td0g/high_speed_flash/MK1_Edgerton/STL/LED Clamp.STL

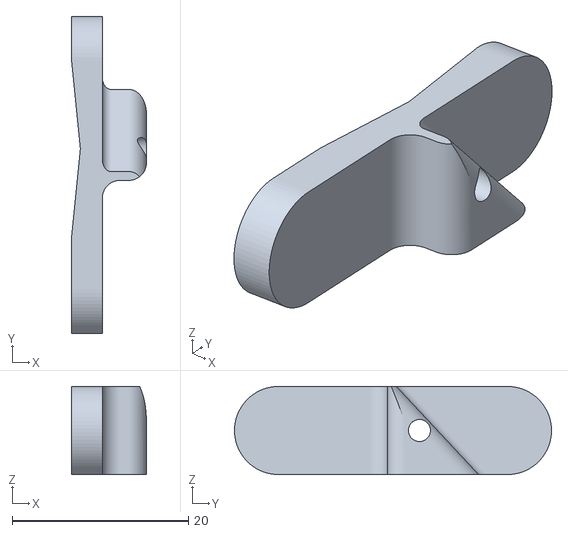
[picture p15: CAD file, 2020-08-31]
MK1_Edgerton/STL/LED Clamp.STL
8.50 x 36.0 x 10.0
