td0g/high_speed_flash/Test Data/2020-08-01/105mm Test/066_Nikon SB-800_64_1.png

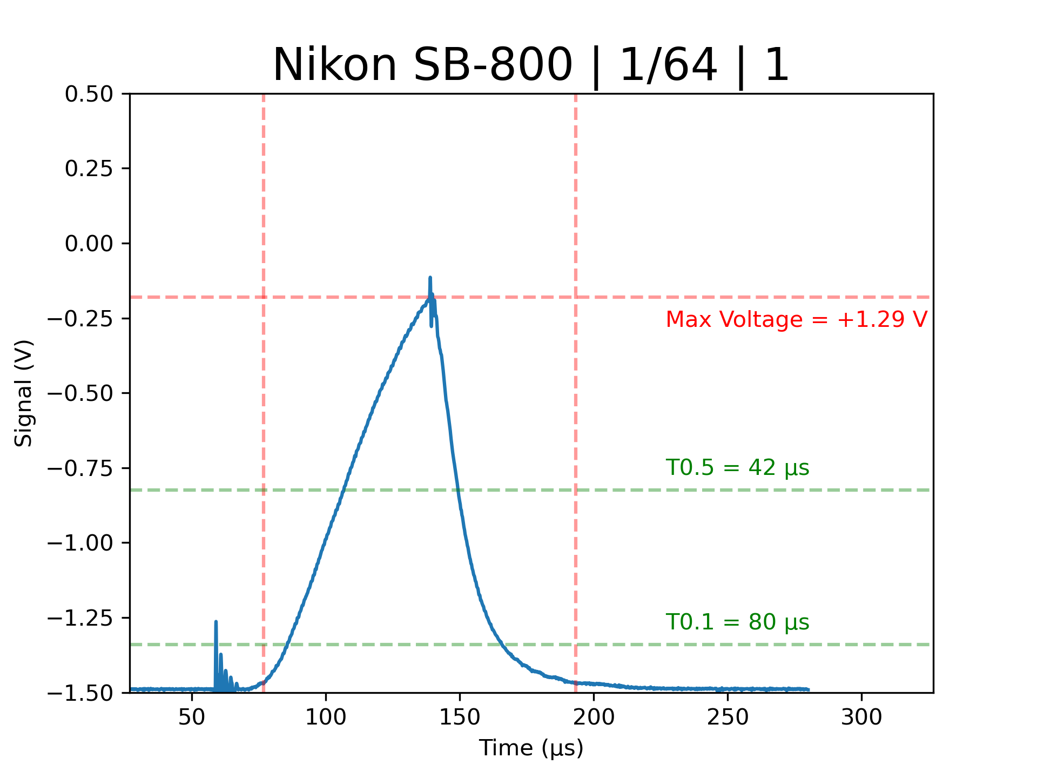
Test Data/2020-08-01/105mm Test/066_Nikon SB-800_64_1.png
