td0g/high_speed_flash/Test Data/2020-08-01/105mm Test/076_Nikon SB-800_32_2.png

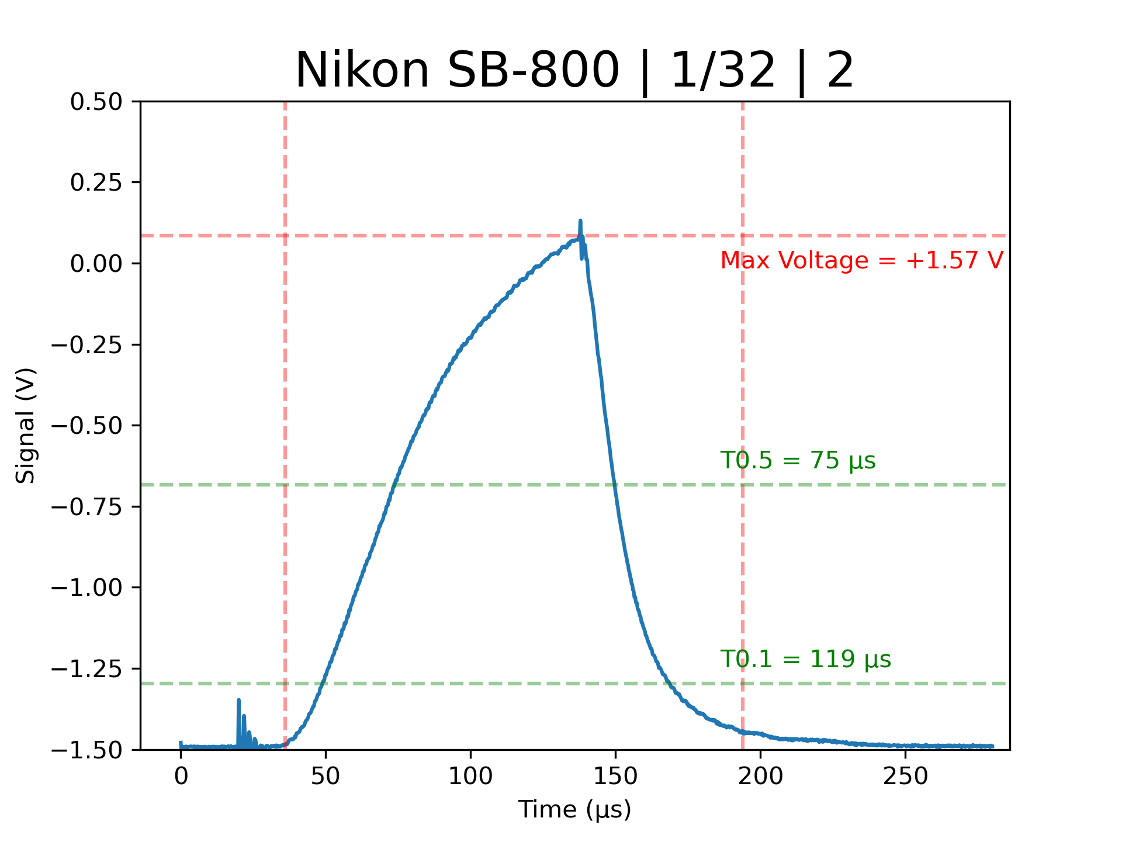
Test Data/2020-08-01/105mm Test/076_Nikon SB-800_32_2.png
