td0g/high_speed_flash/Test Data/2020-08-01/105mm Test/079_Nikon SB-800 105mm_128_1.png

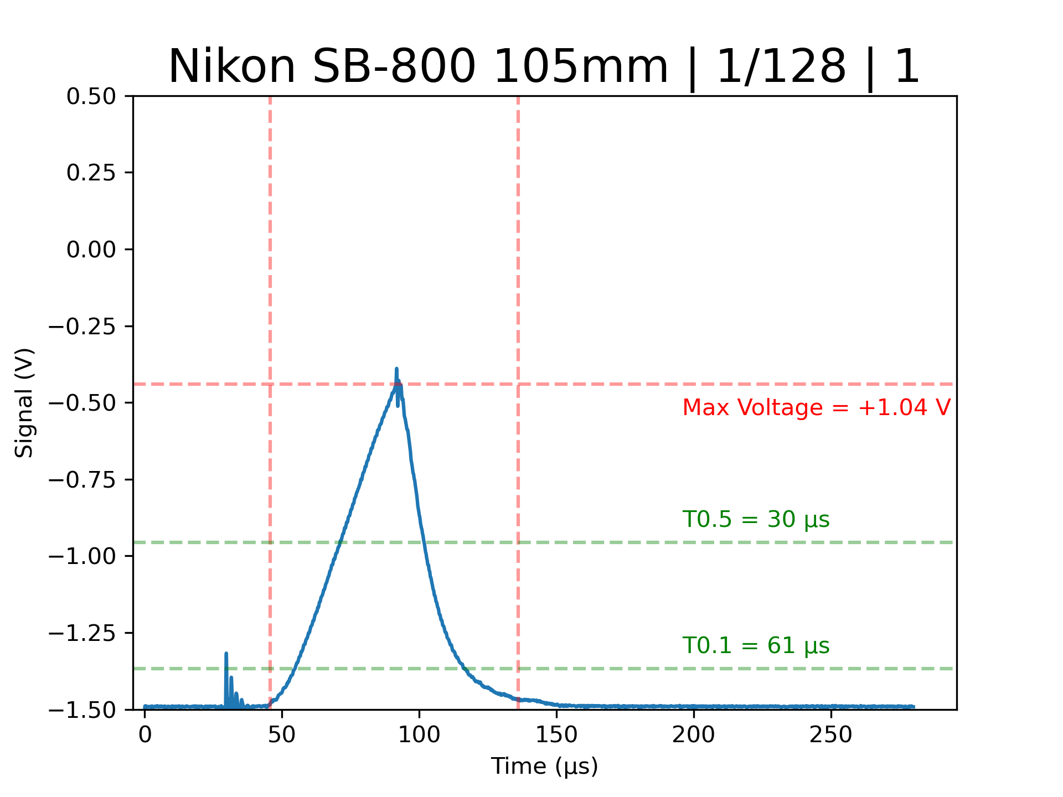
Test Data/2020-08-01/105mm Test/079_Nikon SB-800 105mm_128_1.png
