td0g/high_speed_flash/Test Data/2020-08-01/105mm Test/087_Nikon SB-800 105mm_16_1.png

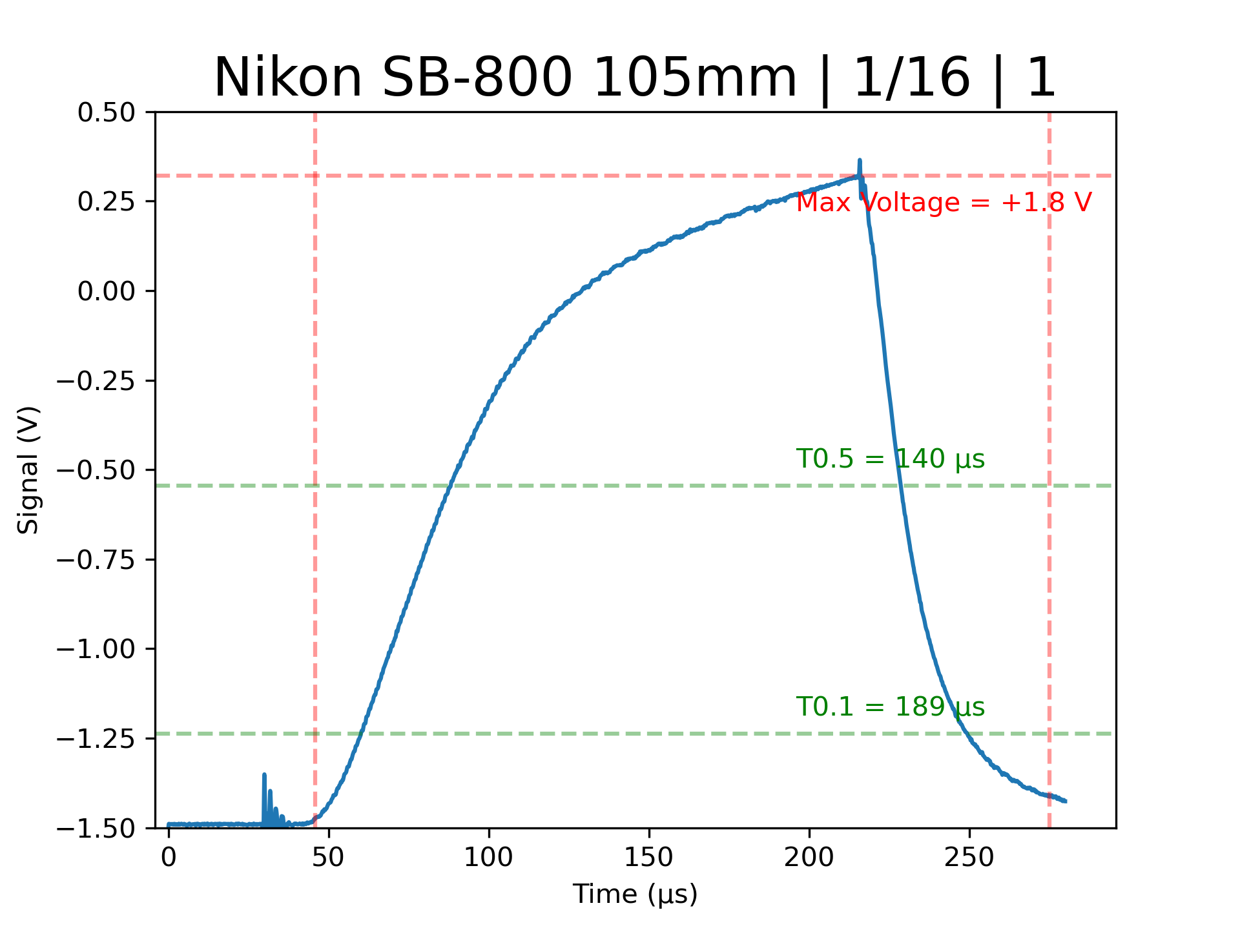
Test Data/2020-08-01/105mm Test/087_Nikon SB-800 105mm_16_1.png
