td0g/high_speed_flash/Test Data/2020-08-01/105mm Test/_MODEL Nikon SB-800 105mm.png

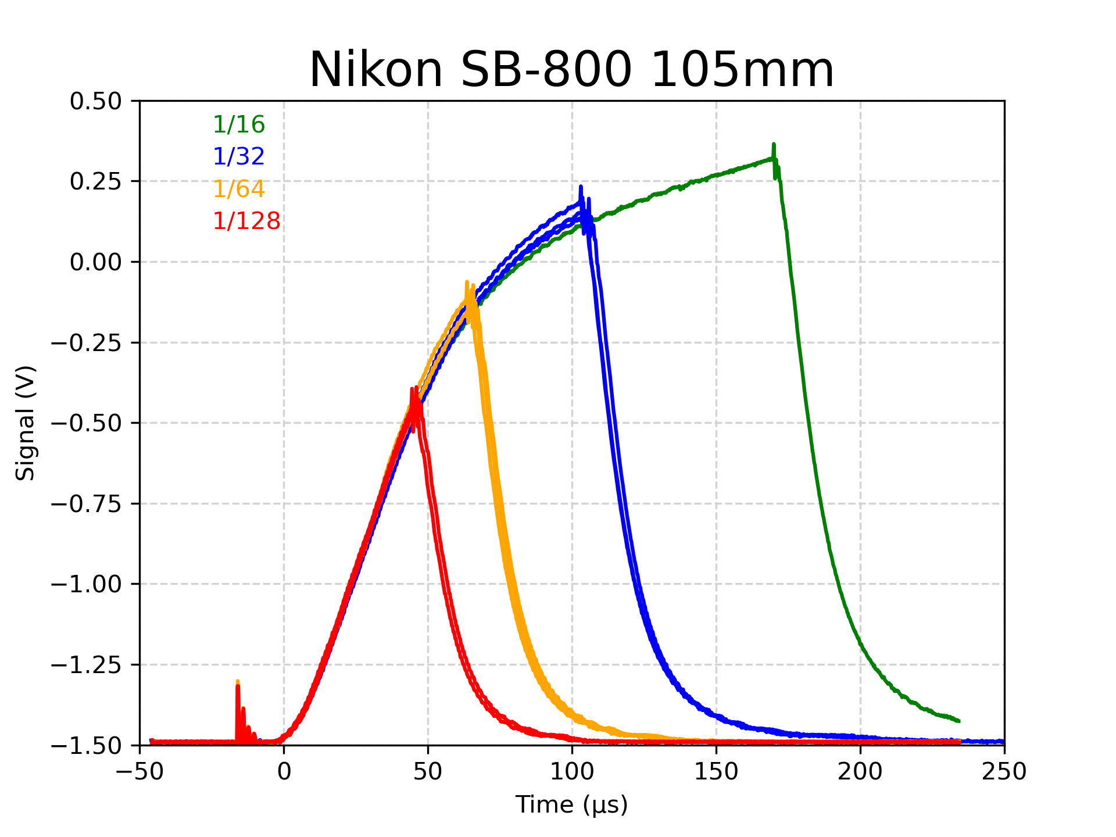
Test Data/2020-08-01/105mm Test/_MODEL Nikon SB-800 105mm.png
