td0g/high_speed_flash/Test Data/2020-08-01/105mm Test/_POWER 3.png

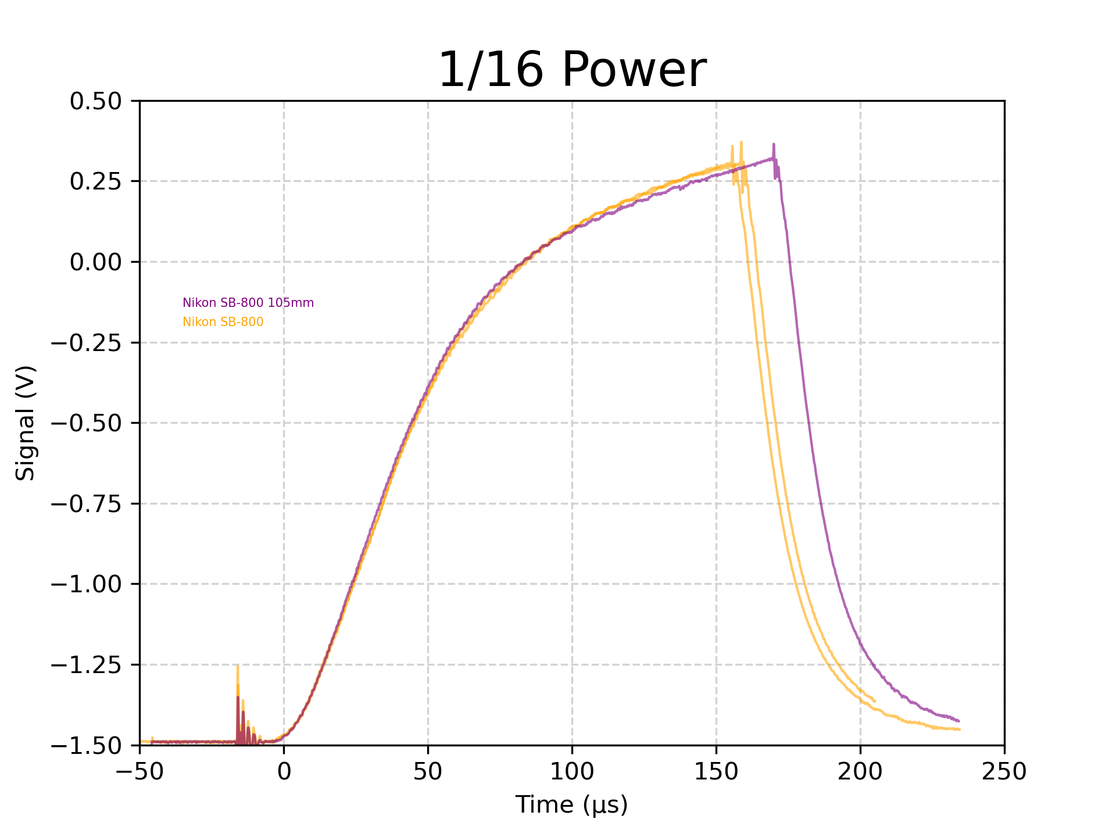
Test Data/2020-08-01/105mm Test/_POWER 3.png
