td0g/high_speed_flash/Test Data/2020-08-01/Removed/002_Nikon SB-800 wCactus_LO_2.png

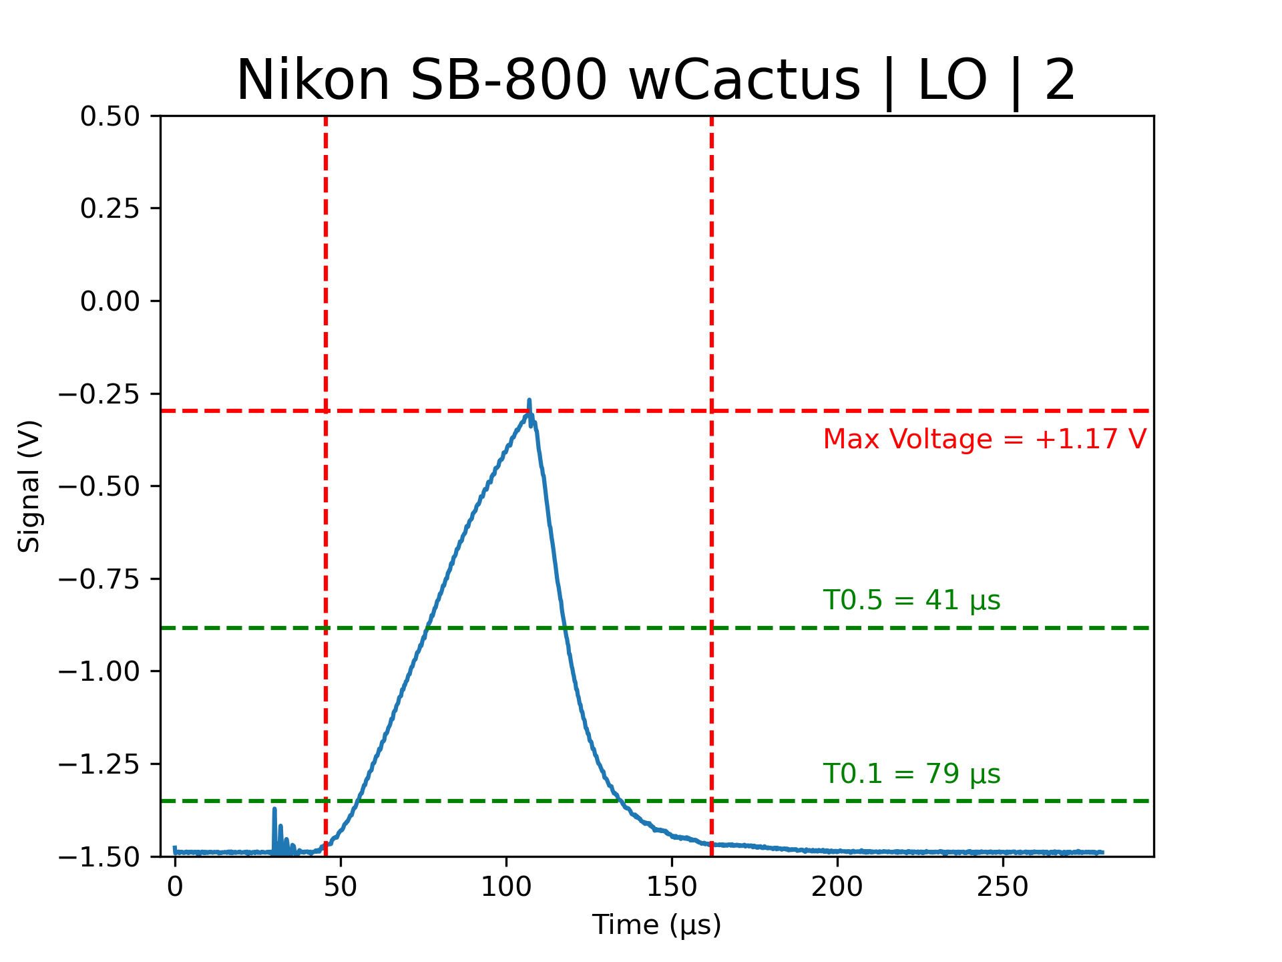
Test Data/2020-08-01/Removed/002_Nikon SB-800 wCactus_LO_2.png
