td0g/high_speed_flash/Test Data/2020-08-01/Removed/004_Nikon SB-800 wCactus_128_1.png

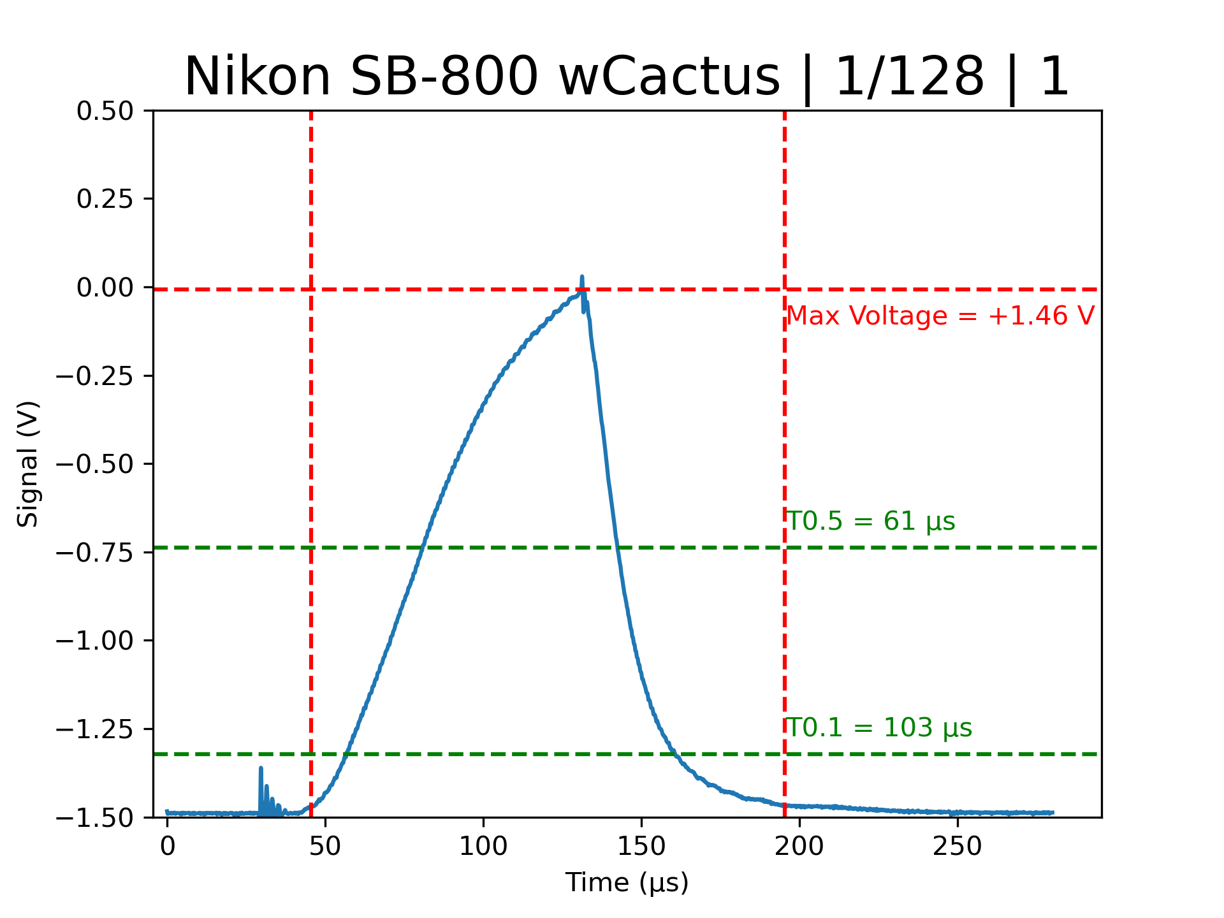
Test Data/2020-08-01/Removed/004_Nikon SB-800 wCactus_128_1.png
