td0g/high_speed_flash/Test Data/2020-08-01/Removed/007_Nikon SB-800 wCactus_64_1.png

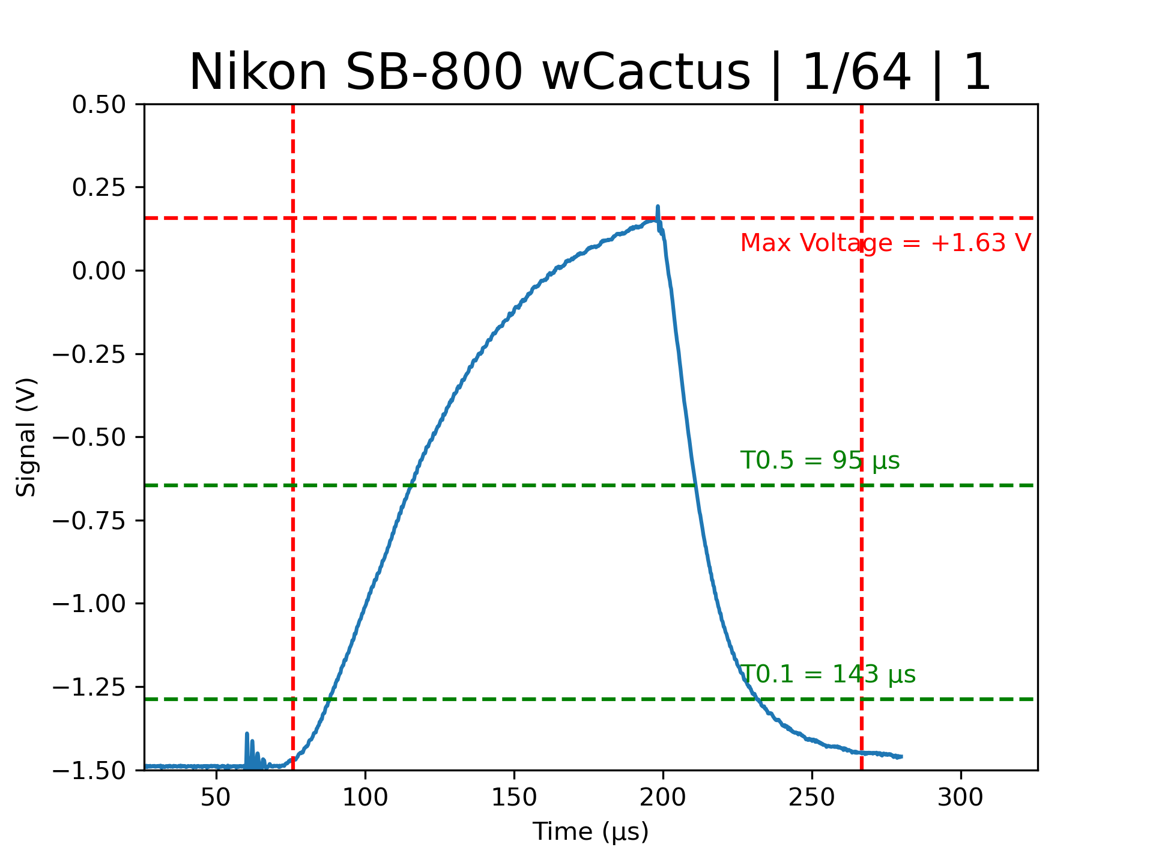
Test Data/2020-08-01/Removed/007_Nikon SB-800 wCactus_64_1.png
