td0g/high_speed_flash/Test Data/2020-08-01/Removed/_MODEL Nikon SB-800.png

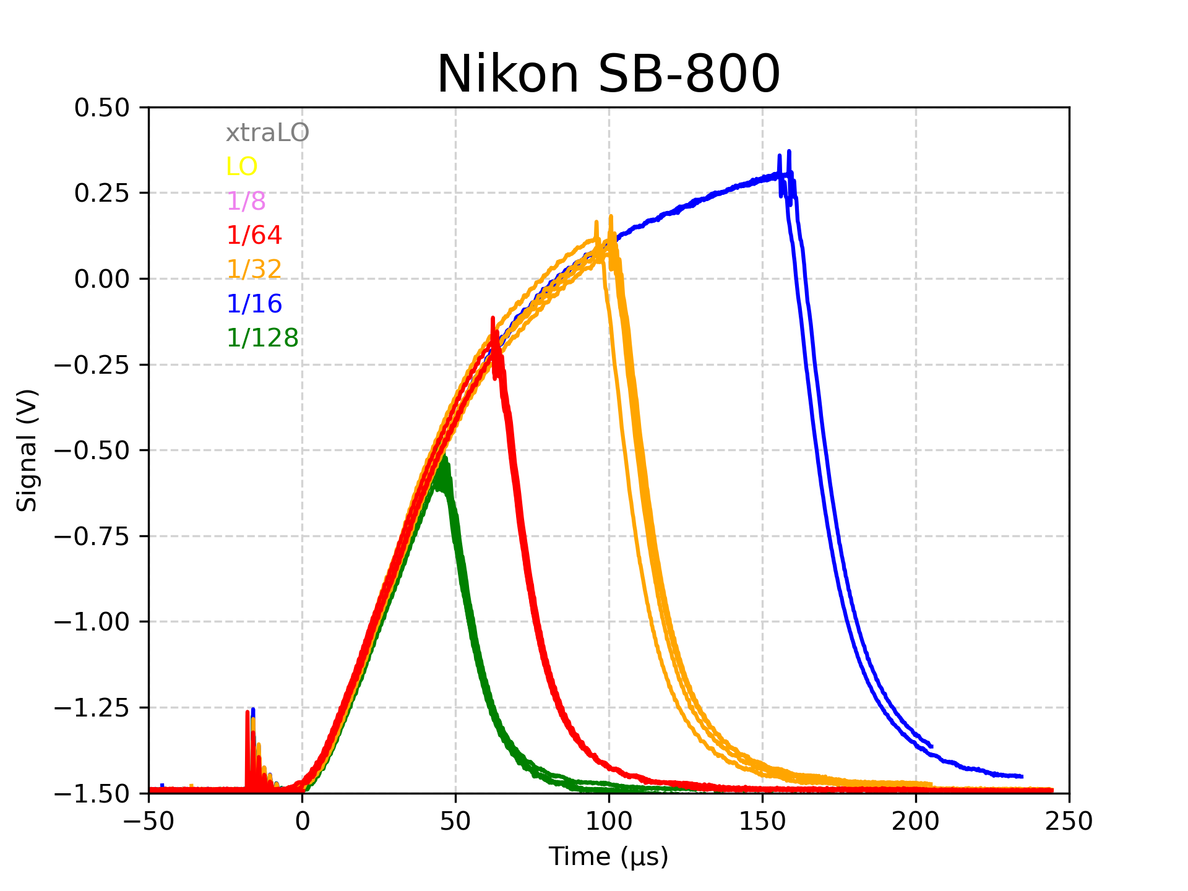
Test Data/2020-08-01/Removed/_MODEL Nikon SB-800.png
