td0g/high_speed_flash/Test Data/2020-08-01/Traces/014_Yongnuo YN-460II_128_3.png

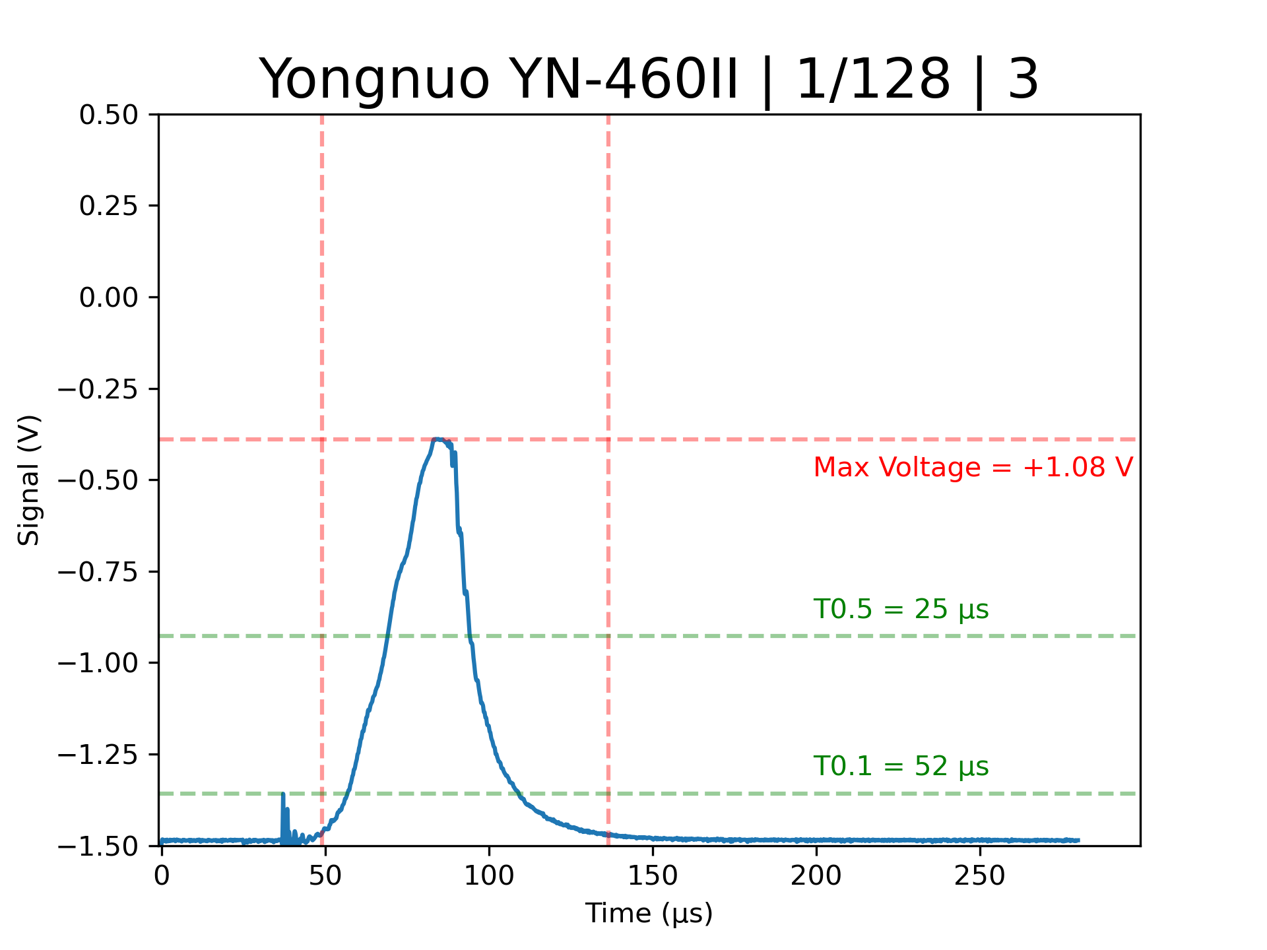
Test Data/2020-08-01/Traces/014_Yongnuo YN-460II_128_3.png
