td0g/high_speed_flash/Test Data/2020-08-01/Traces/015_Yongnuo YN-460II_64_1.png

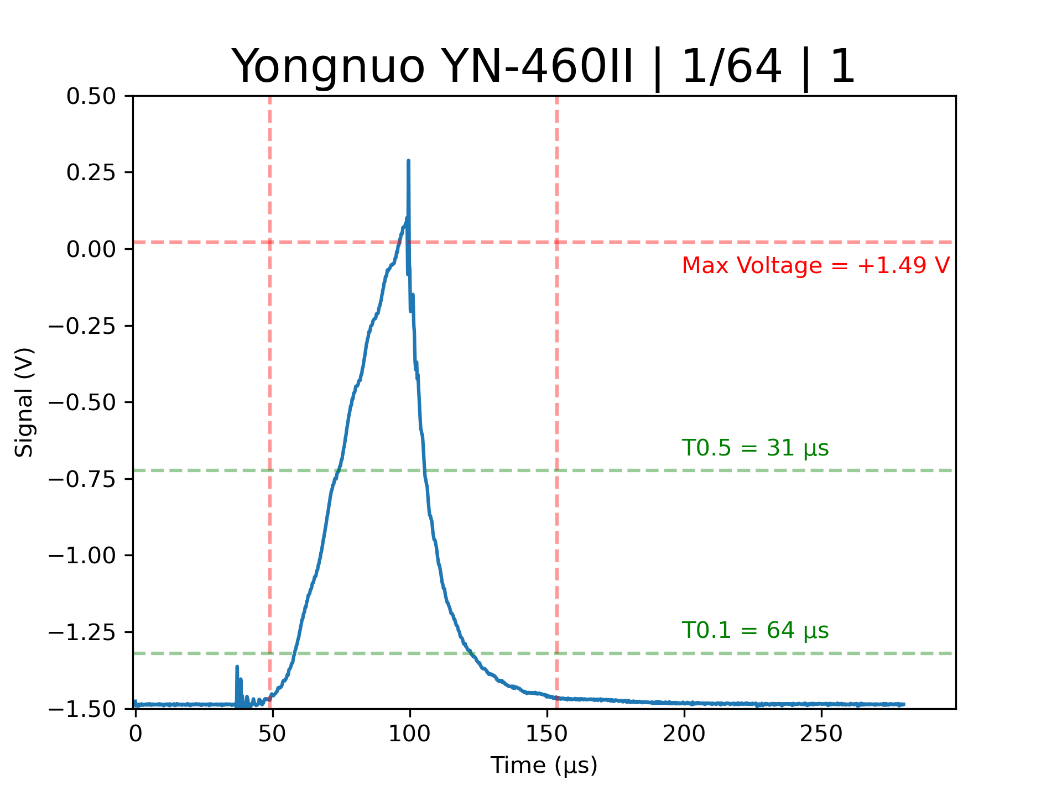
Test Data/2020-08-01/Traces/015_Yongnuo YN-460II_64_1.png
