td0g/high_speed_flash/Test Data/2020-08-01/Traces/018_Yongnuo YN-460II_32_1.png

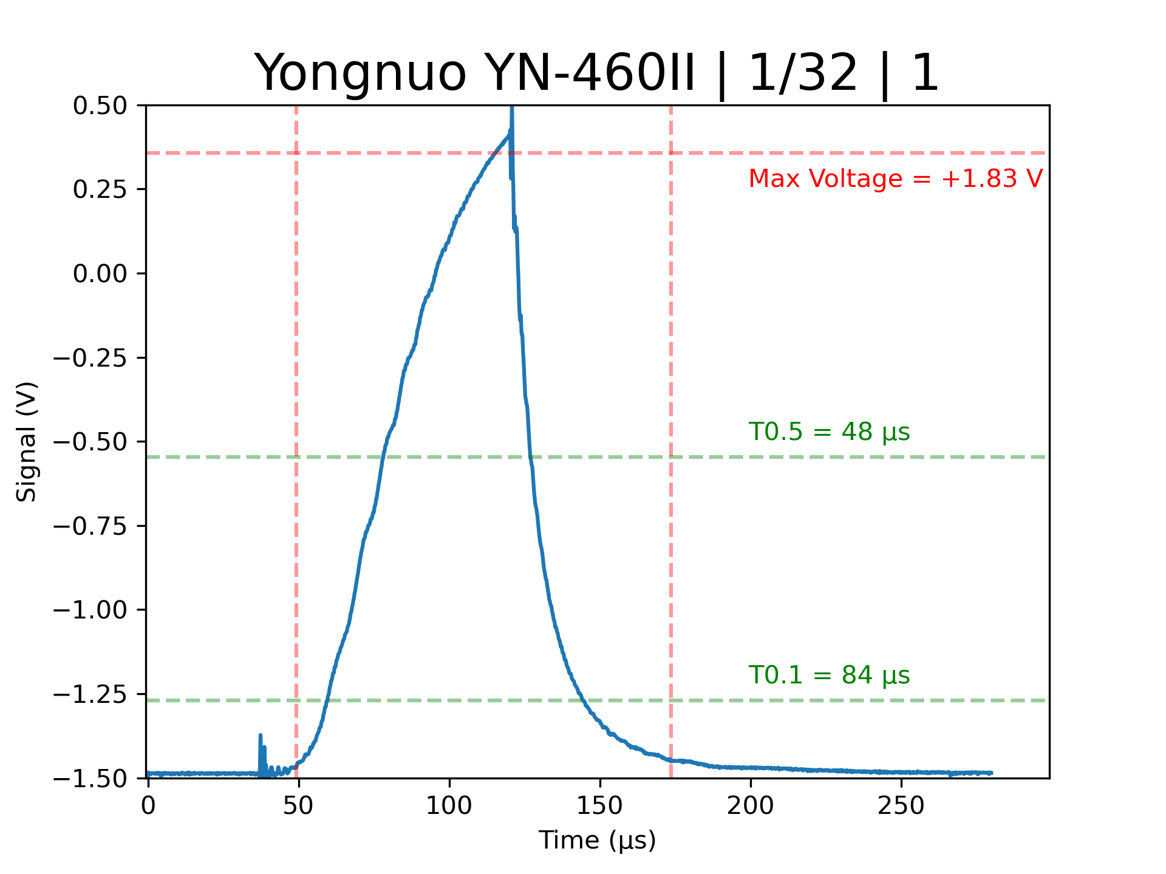
Test Data/2020-08-01/Traces/018_Yongnuo YN-460II_32_1.png
