td0g/high_speed_flash/Test Data/2020-08-01/Traces/019_Canon 430EX-II wCactus_LO_1.png

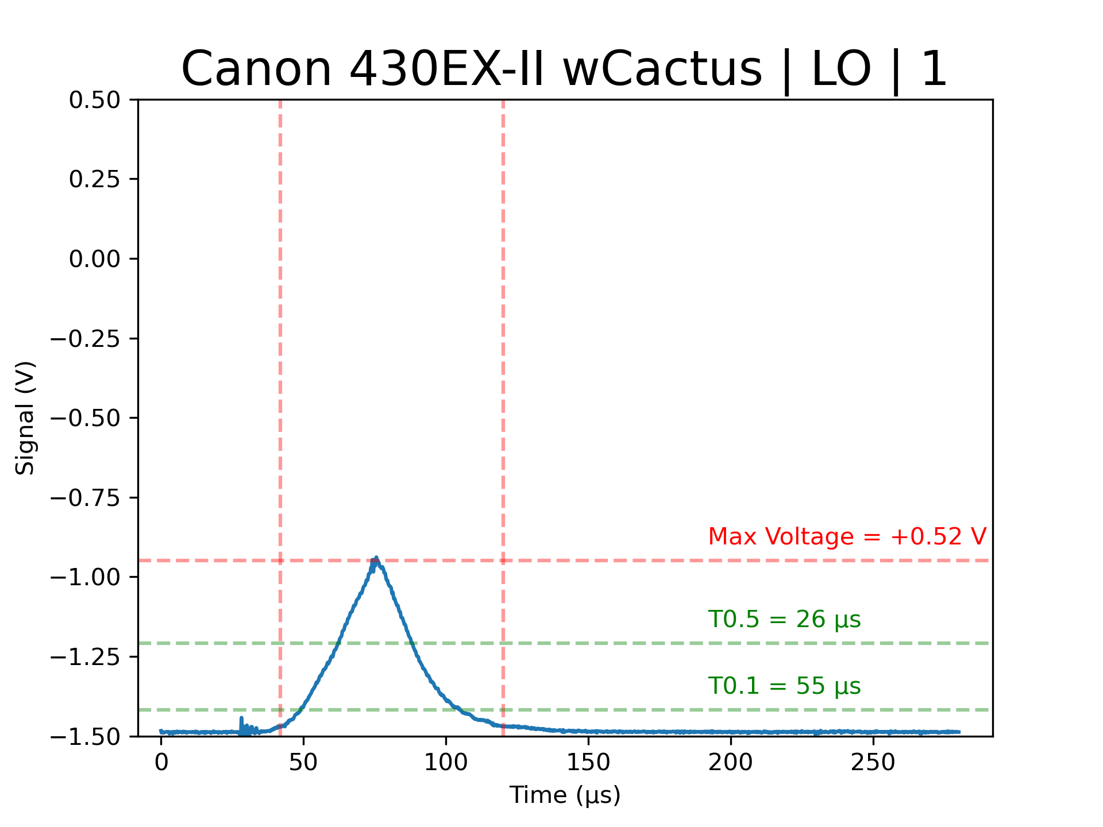
Test Data/2020-08-01/Traces/019_Canon 430EX-II wCactus_LO_1.png
