td0g/high_speed_flash/Test Data/2020-08-01/Traces/020_Canon 430EX-II wCactus_LO_2.png

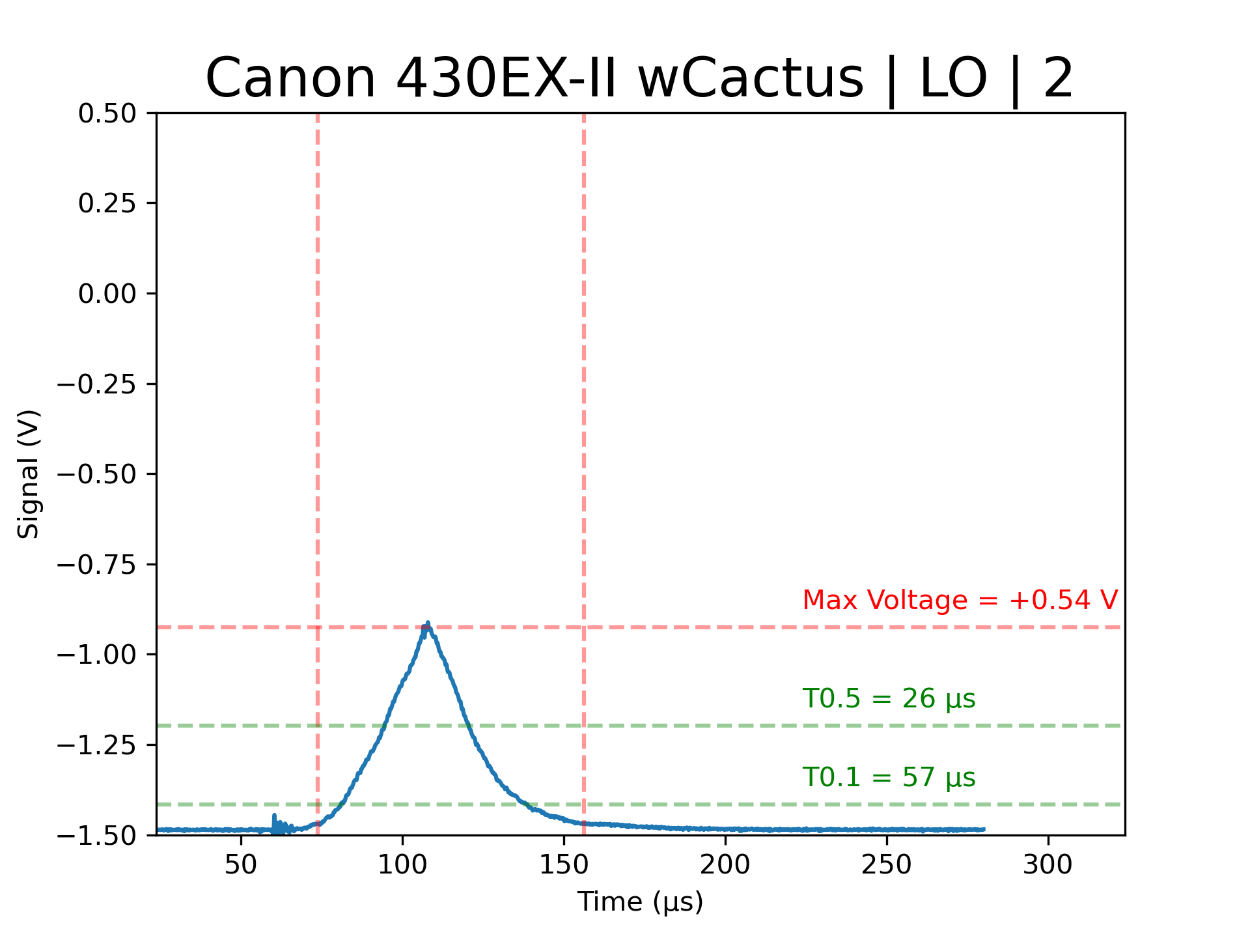
Test Data/2020-08-01/Traces/020_Canon 430EX-II wCactus_LO_2.png
