td0g/high_speed_flash/Test Data/2020-08-01/Traces/025_Canon 430EX-II wCactus_64_1.png

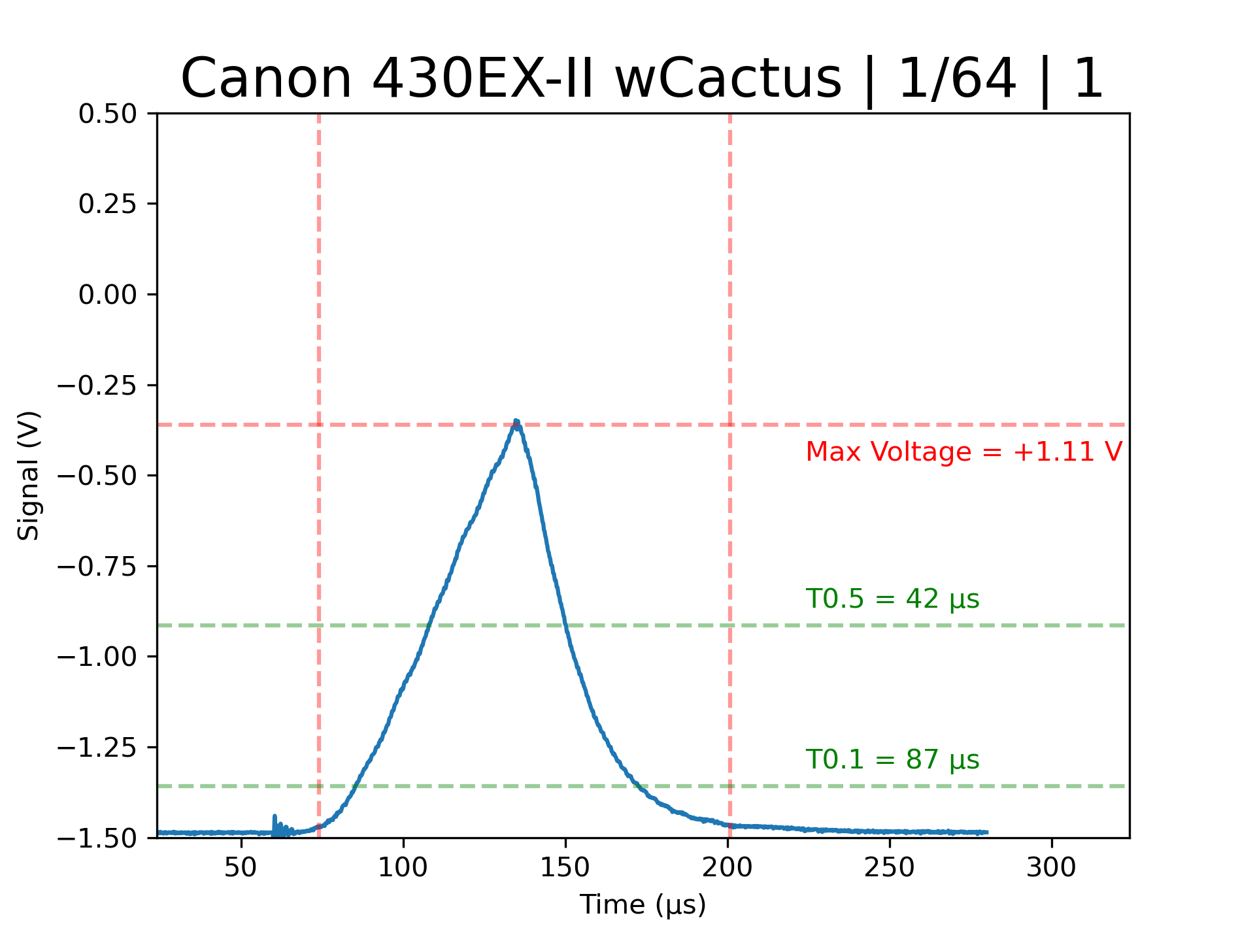
Test Data/2020-08-01/Traces/025_Canon 430EX-II wCactus_64_1.png
