td0g/high_speed_flash/Test Data/2020-08-01/Traces/031_Canon 430EX-II wCactus_32_1.png

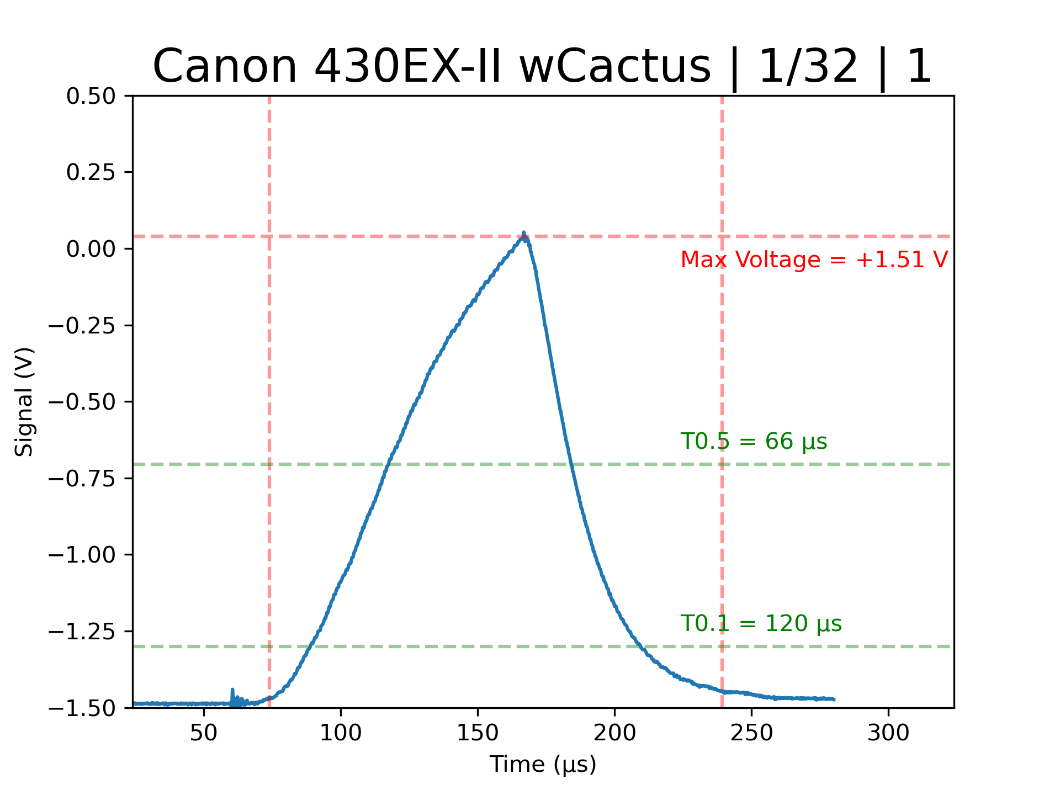
Test Data/2020-08-01/Traces/031_Canon 430EX-II wCactus_32_1.png
