td0g/high_speed_flash/Test Data/2020-08-01/Traces/035_Nikon SB-910 wCactus_LO_1.png

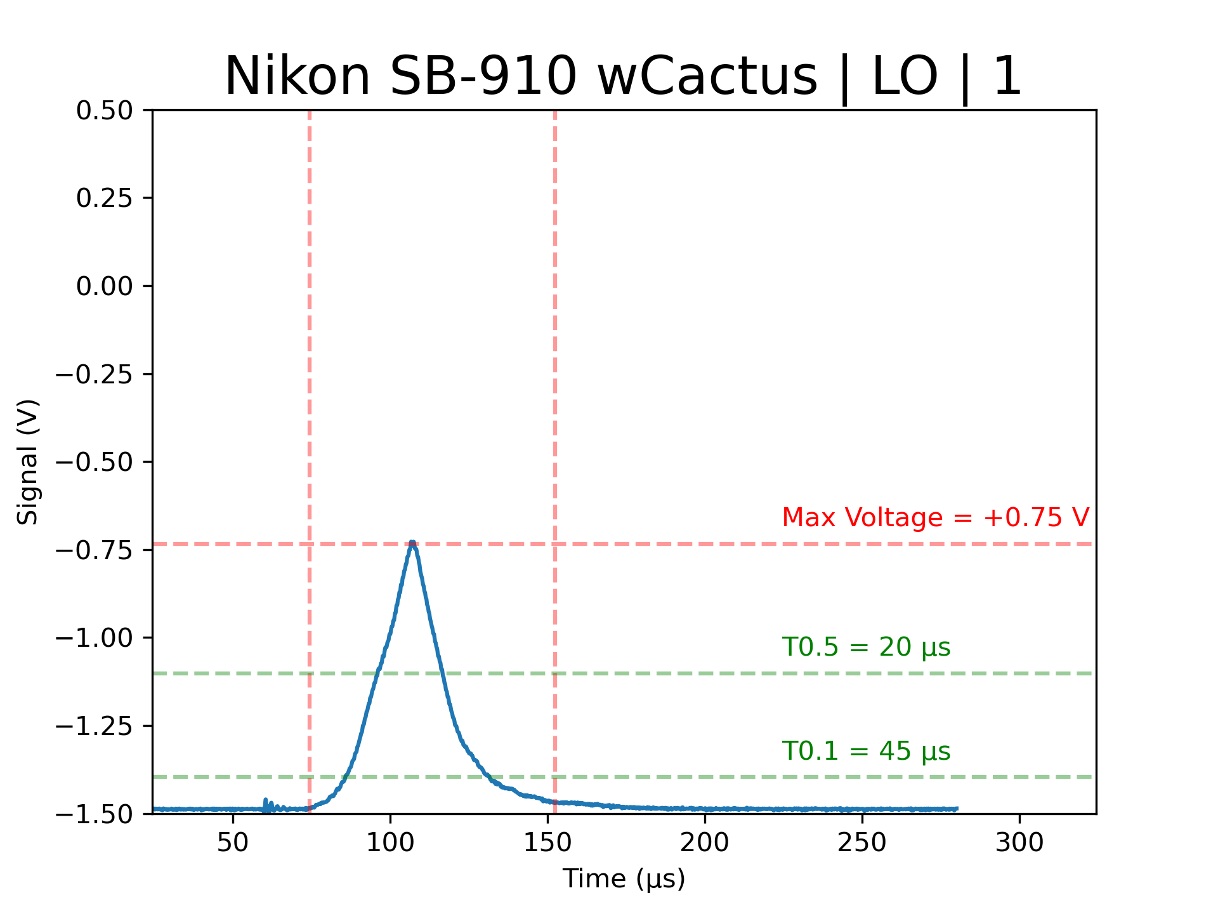
Test Data/2020-08-01/Traces/035_Nikon SB-910 wCactus_LO_1.png
