td0g/high_speed_flash/Test Data/2020-08-01/Traces/045_Nikon SB-910 wCactus_32_2.png

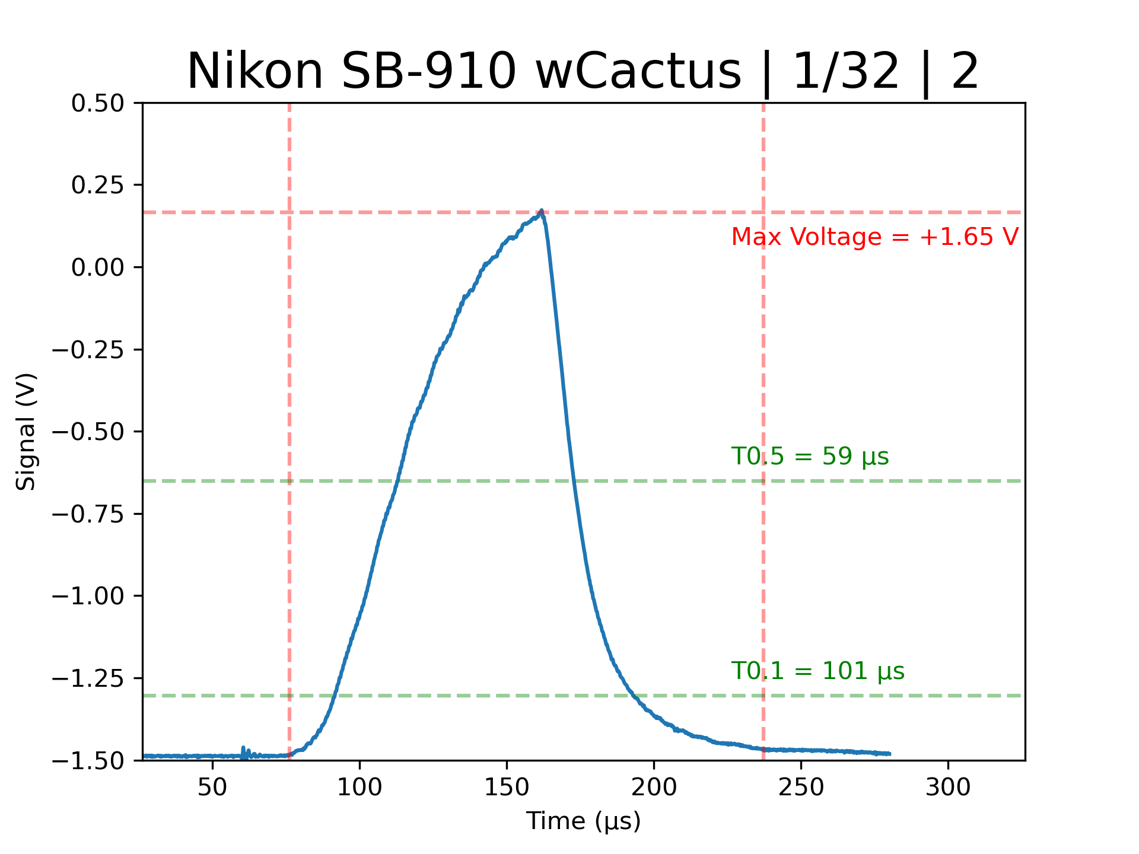
Test Data/2020-08-01/Traces/045_Nikon SB-910 wCactus_32_2.png
