td0g/high_speed_flash/Test Data/2020-08-01/Traces/047_Nikon SB-910 wCactus_16_1.png

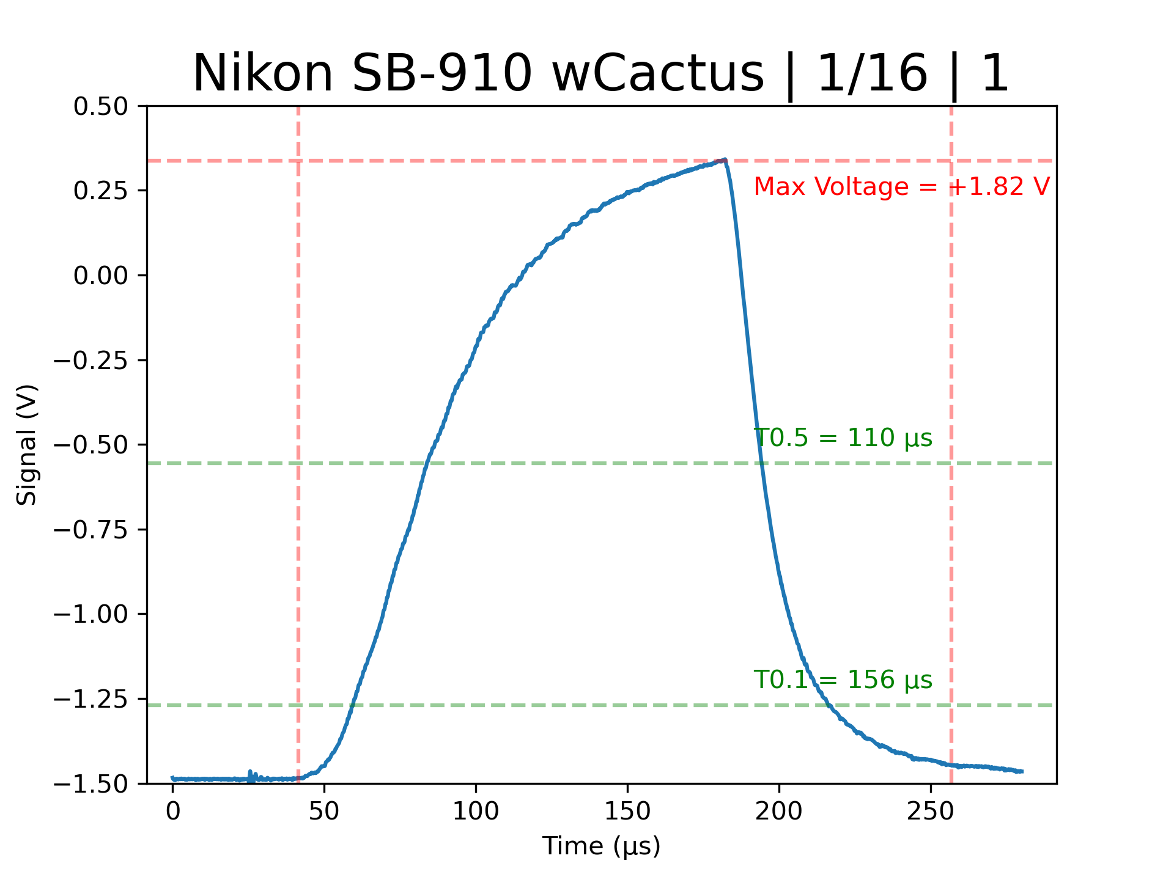
Test Data/2020-08-01/Traces/047_Nikon SB-910 wCactus_16_1.png
