td0g/high_speed_flash/Test Data/2020-08-01/Traces/049_Nikon SB-800 wCactus_xtraLO_1.png

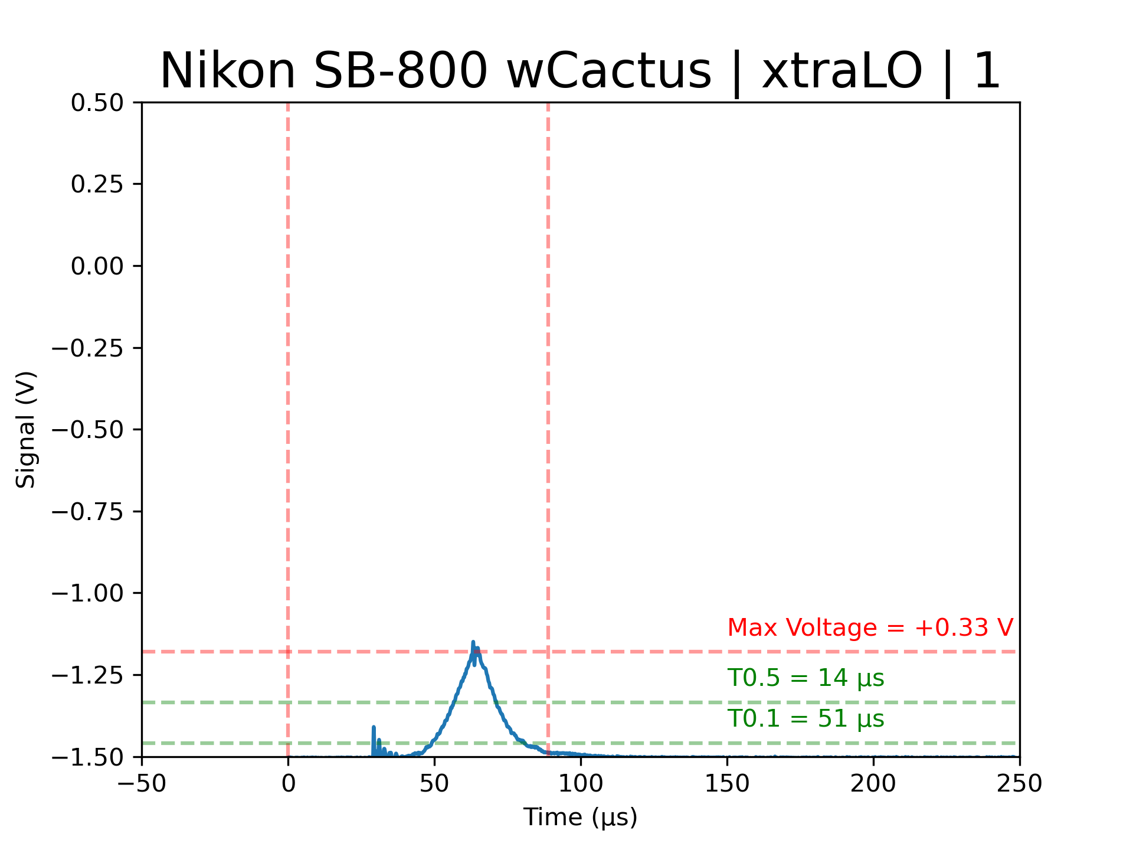
Test Data/2020-08-01/Traces/049_Nikon SB-800 wCactus_xtraLO_1.png
