td0g/high_speed_flash/Test Data/2020-08-01/Traces/061_Nikon SB-800 wCactus_32_1.png

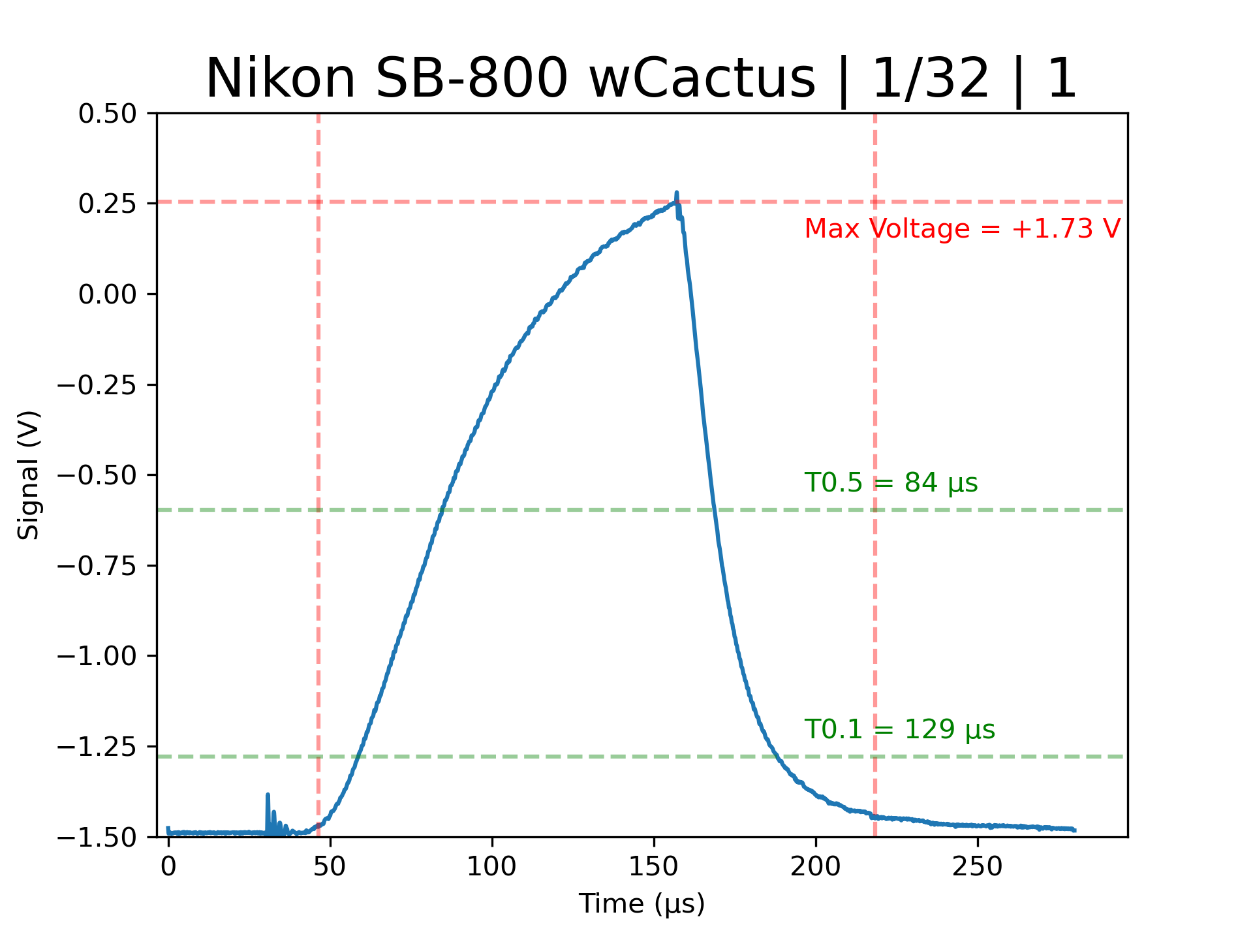
Test Data/2020-08-01/Traces/061_Nikon SB-800 wCactus_32_1.png
