td0g/high_speed_flash/Test Data/2020-08-01/Traces/064_Nikon SB-800 wCactus_16_1.png

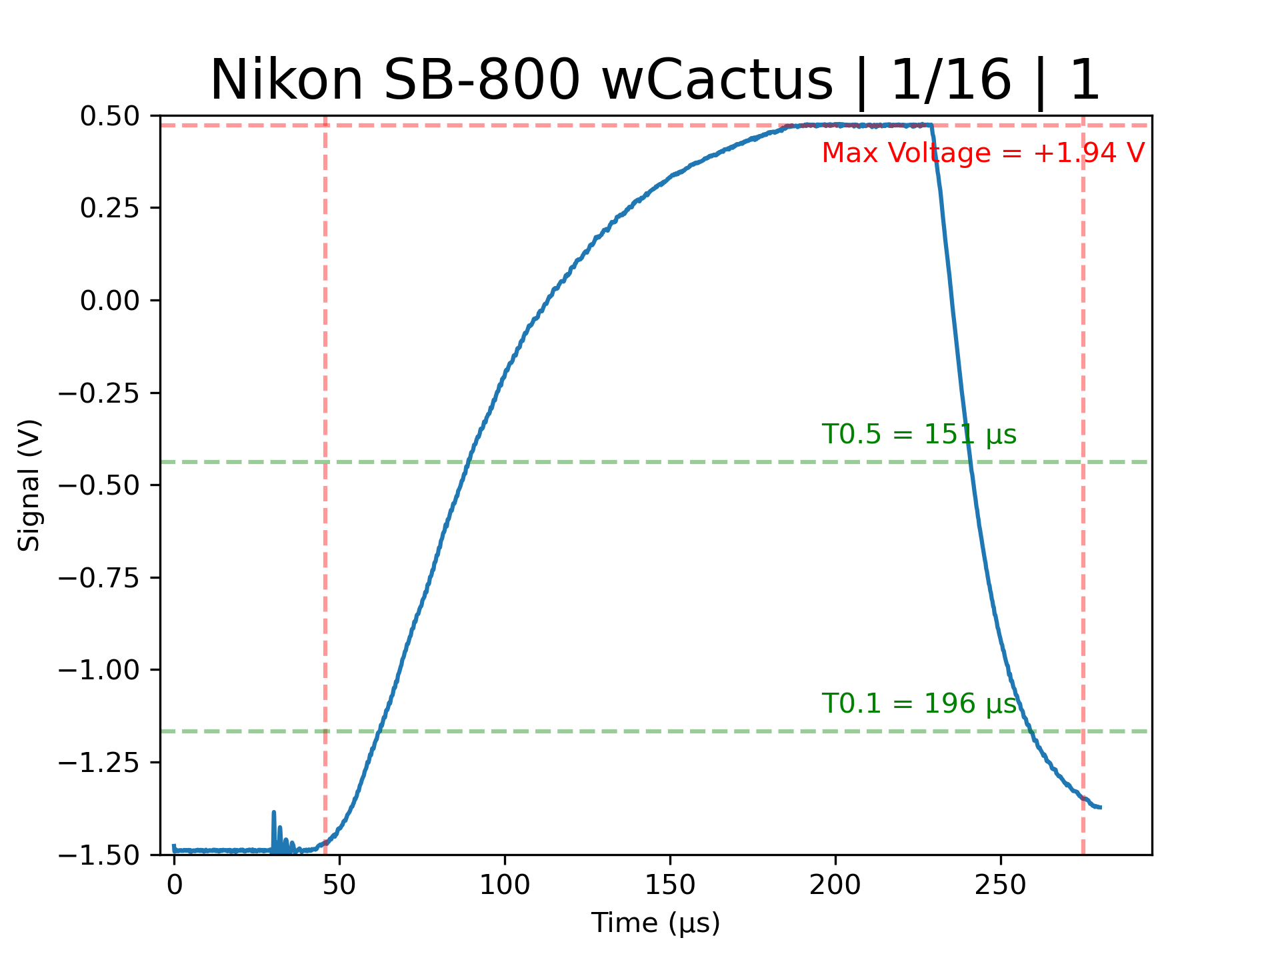
Test Data/2020-08-01/Traces/064_Nikon SB-800 wCactus_16_1.png
