td0g/high_speed_flash/Test Data/2020-08-01/Traces/095_Canon EX430-II_64_1.png

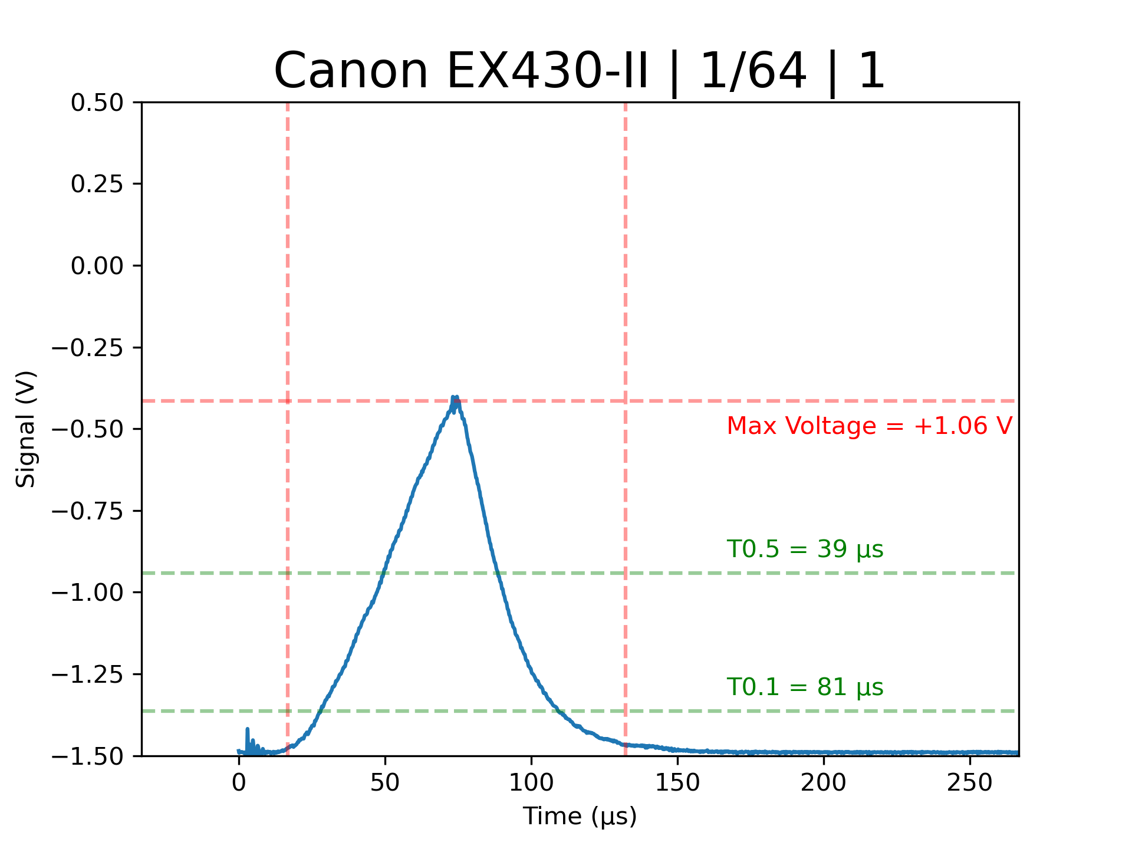
Test Data/2020-08-01/Traces/095_Canon EX430-II_64_1.png
