td0g/high_speed_flash/Test Data/2020-08-01/Traces/099_Canon EX430-II_32_2.png

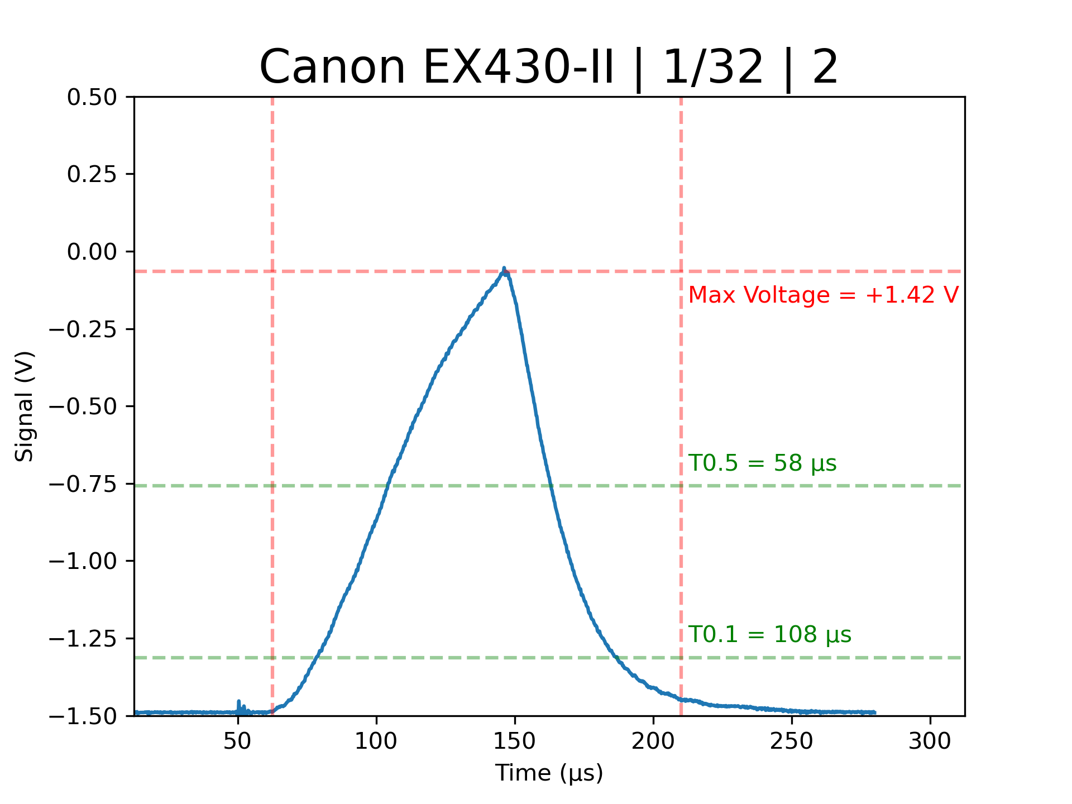
Test Data/2020-08-01/Traces/099_Canon EX430-II_32_2.png
