td0g/high_speed_flash/Test Data/2020-08-01/Traces/100_Canon EX430-II_32_3.png

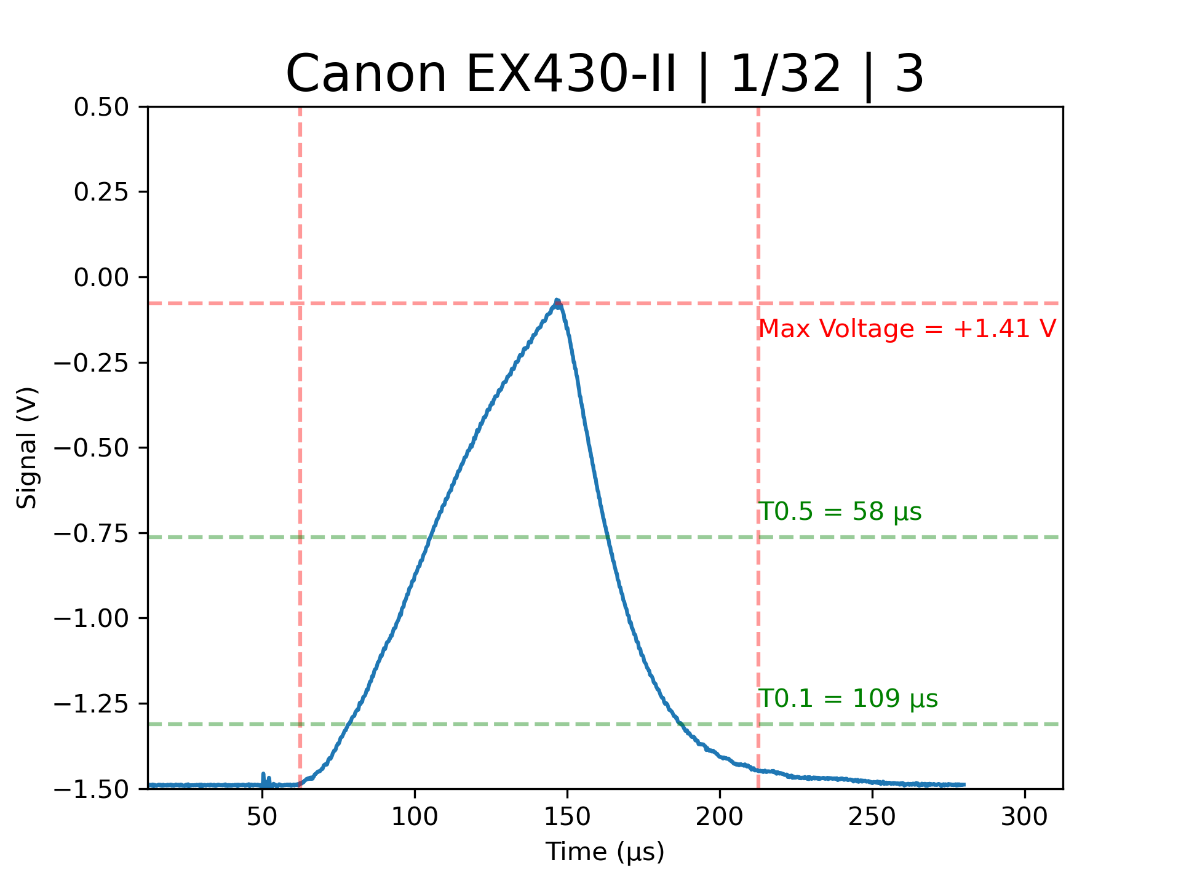
Test Data/2020-08-01/Traces/100_Canon EX430-II_32_3.png
