td0g/high_speed_flash/Test Data/2020-08-01/Traces/101_Canon EX430-II_16_1.png

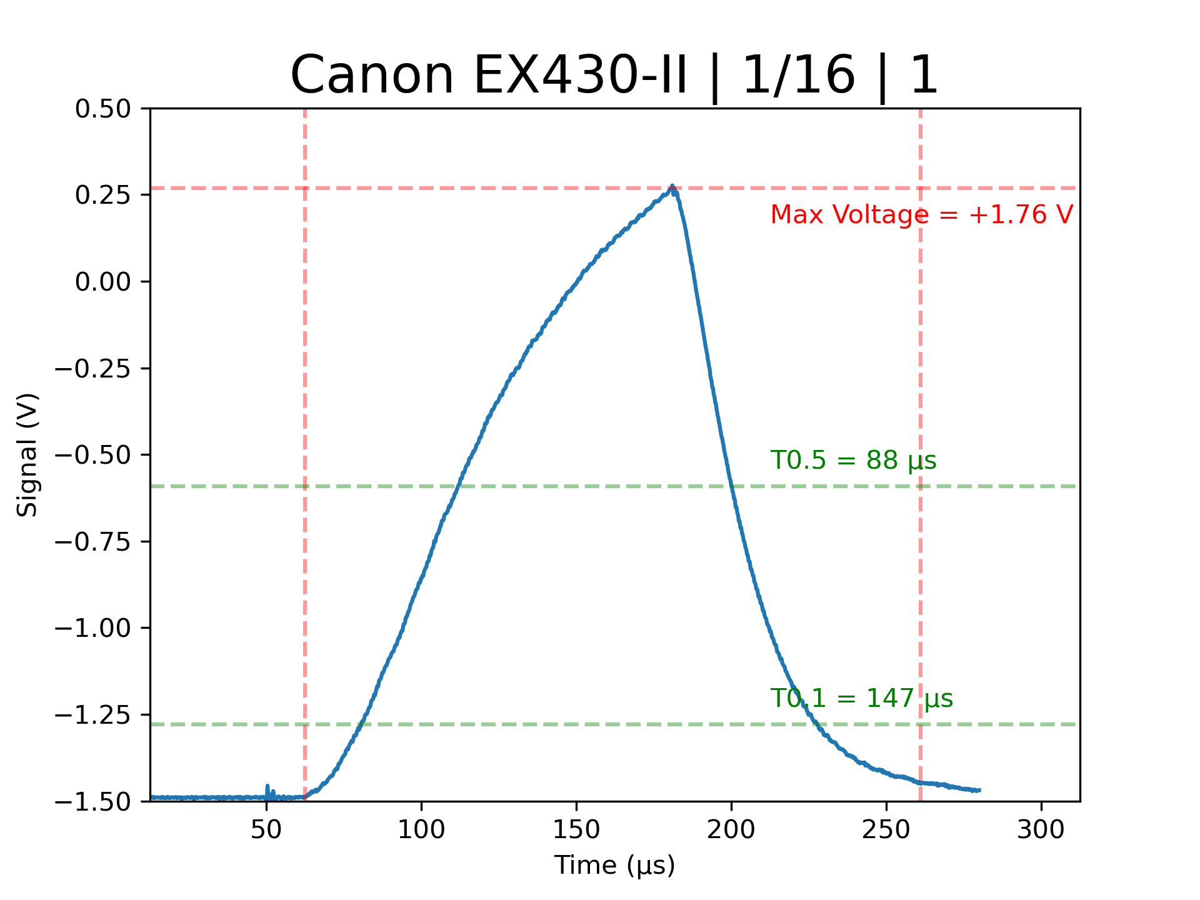
Test Data/2020-08-01/Traces/101_Canon EX430-II_16_1.png
