td0g/high_speed_flash/Test Data/2020-08-01/Traces/104_Canon EX430-II_8_1.png

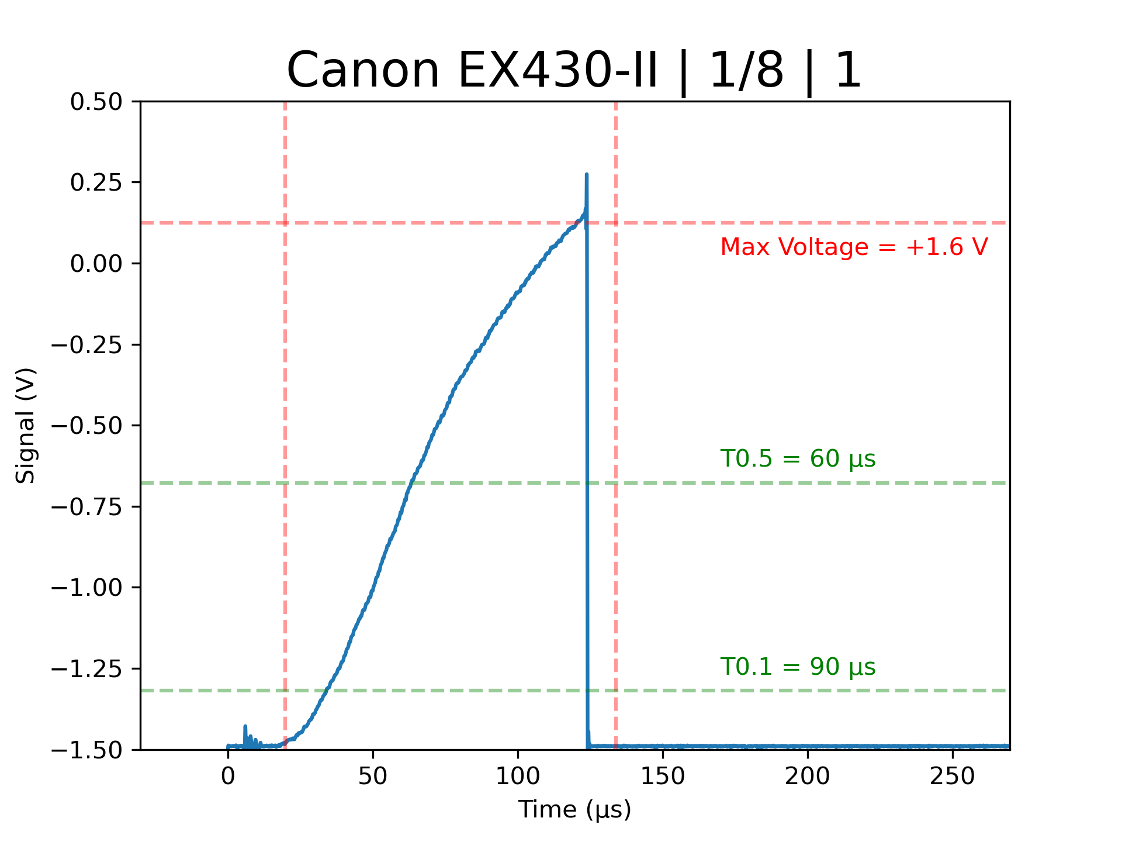
Test Data/2020-08-01/Traces/104_Canon EX430-II_8_1.png
