td0g/high_speed_flash/Test Data/2020-08-01/Traces/111_Nikon SB-910_32_1.png

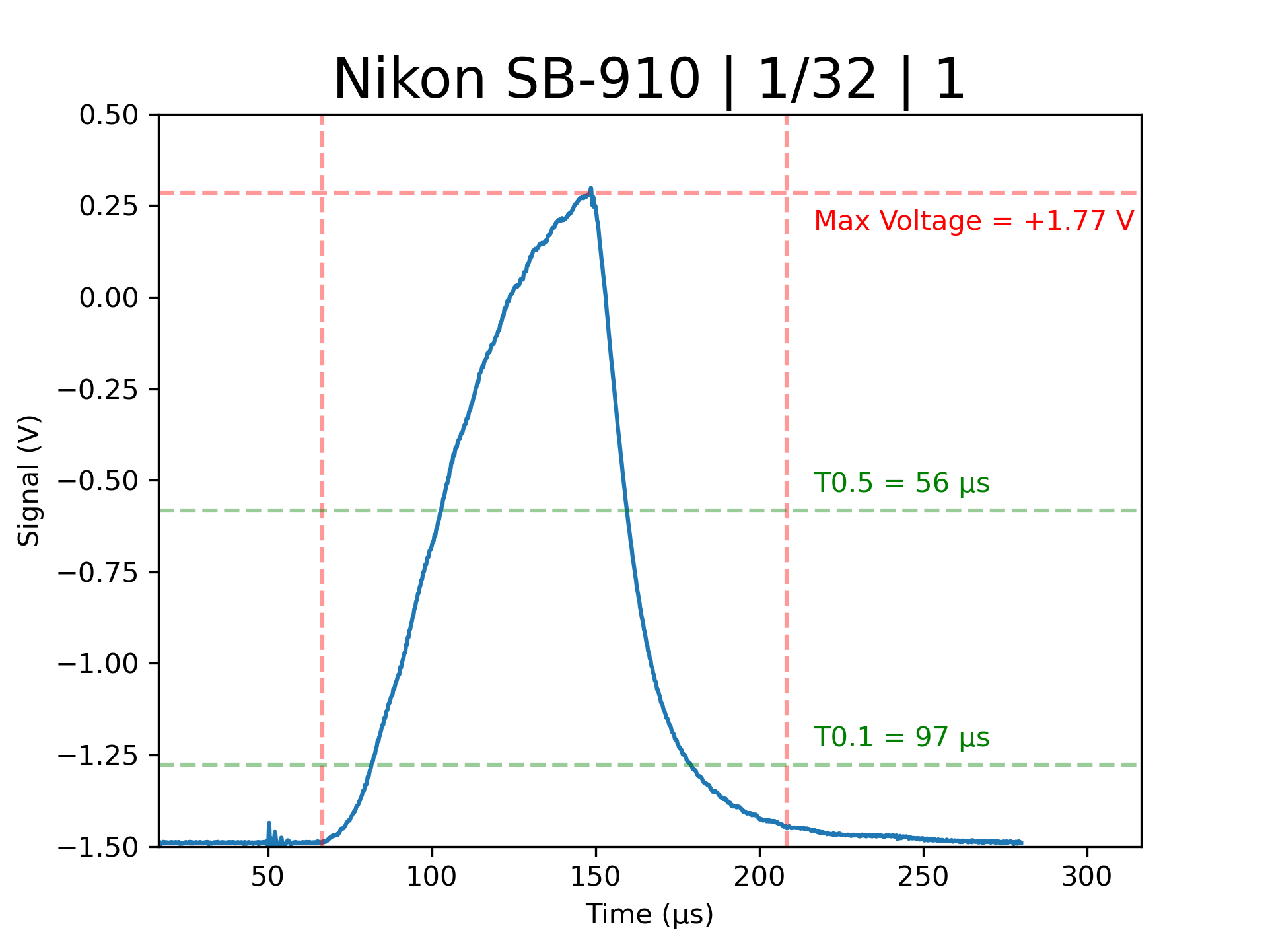
Test Data/2020-08-01/Traces/111_Nikon SB-910_32_1.png
