td0g/high_speed_flash/Test Data/2020-08-01/Traces/112_Nikon SB-910_32_2.png

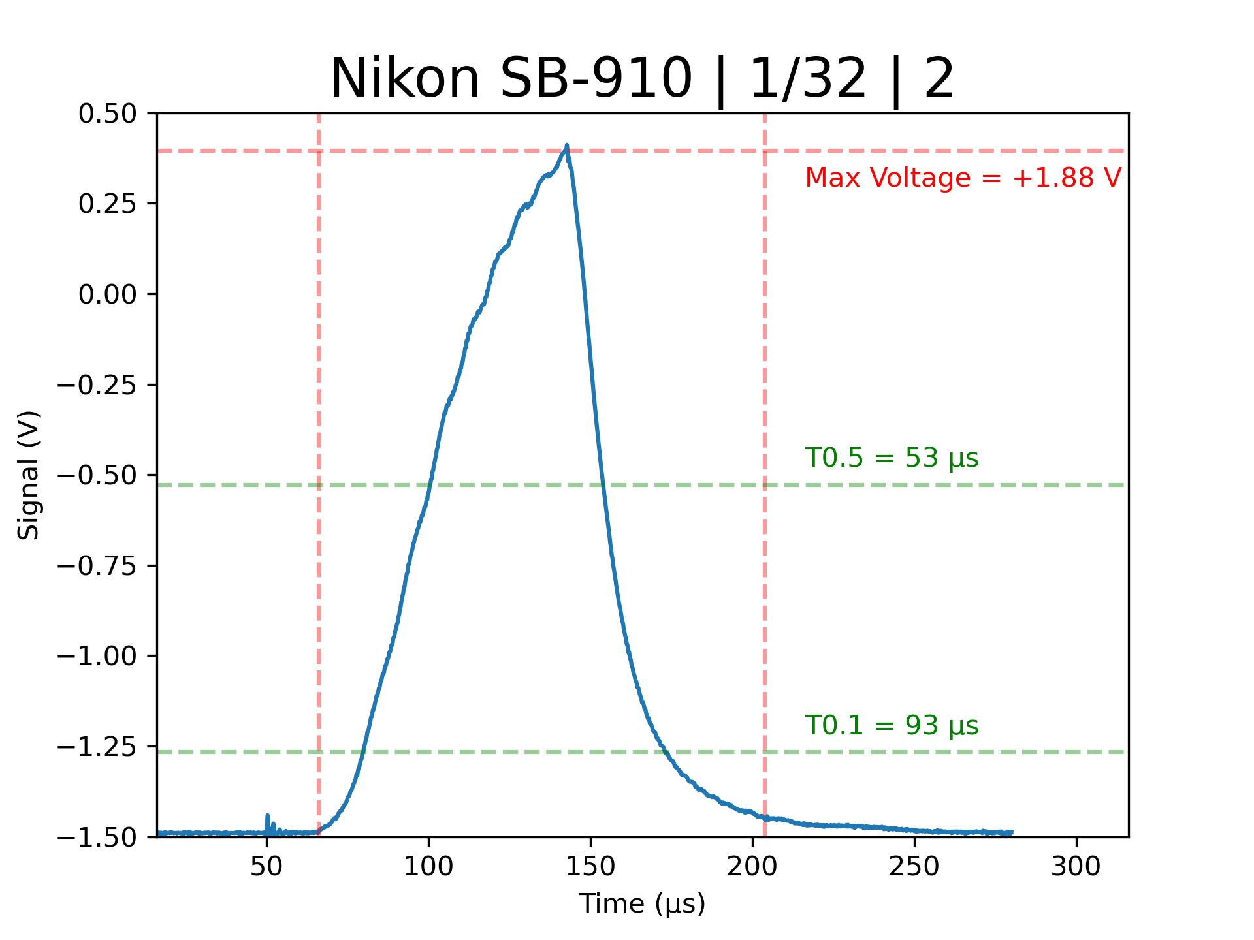
Test Data/2020-08-01/Traces/112_Nikon SB-910_32_2.png
