td0g/high_speed_flash/Test Data/2020-08-01/Traces/113_Nikon SB-910_32_3.png

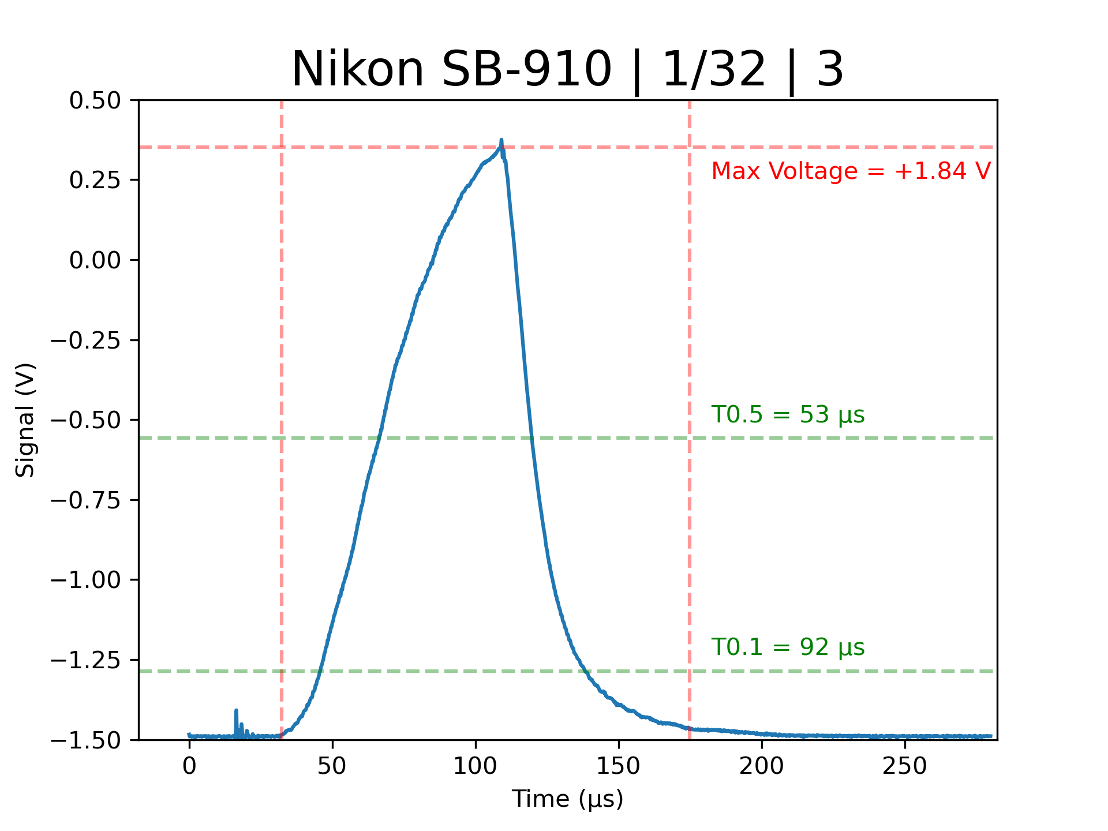
Test Data/2020-08-01/Traces/113_Nikon SB-910_32_3.png
