td0g/high_speed_flash/Test Data/2020-08-01/Traces/_MODEL Canon 430EX-II wCactus.png

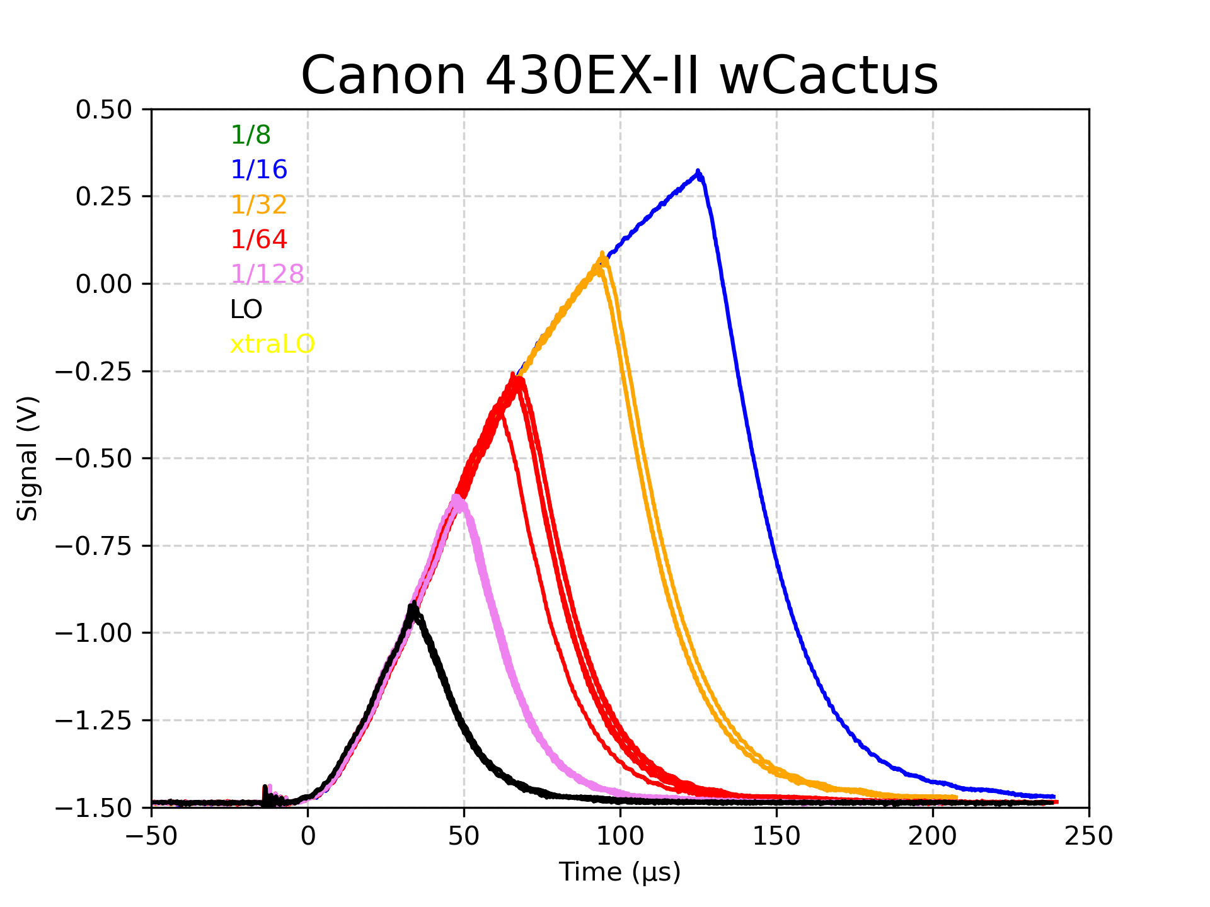
Test Data/2020-08-01/Traces/_MODEL Canon 430EX-II wCactus.png
