td0g/high_speed_flash/Test Data/2020-08-01/Traces/_MODEL Nikon SB-910 wCactus.png

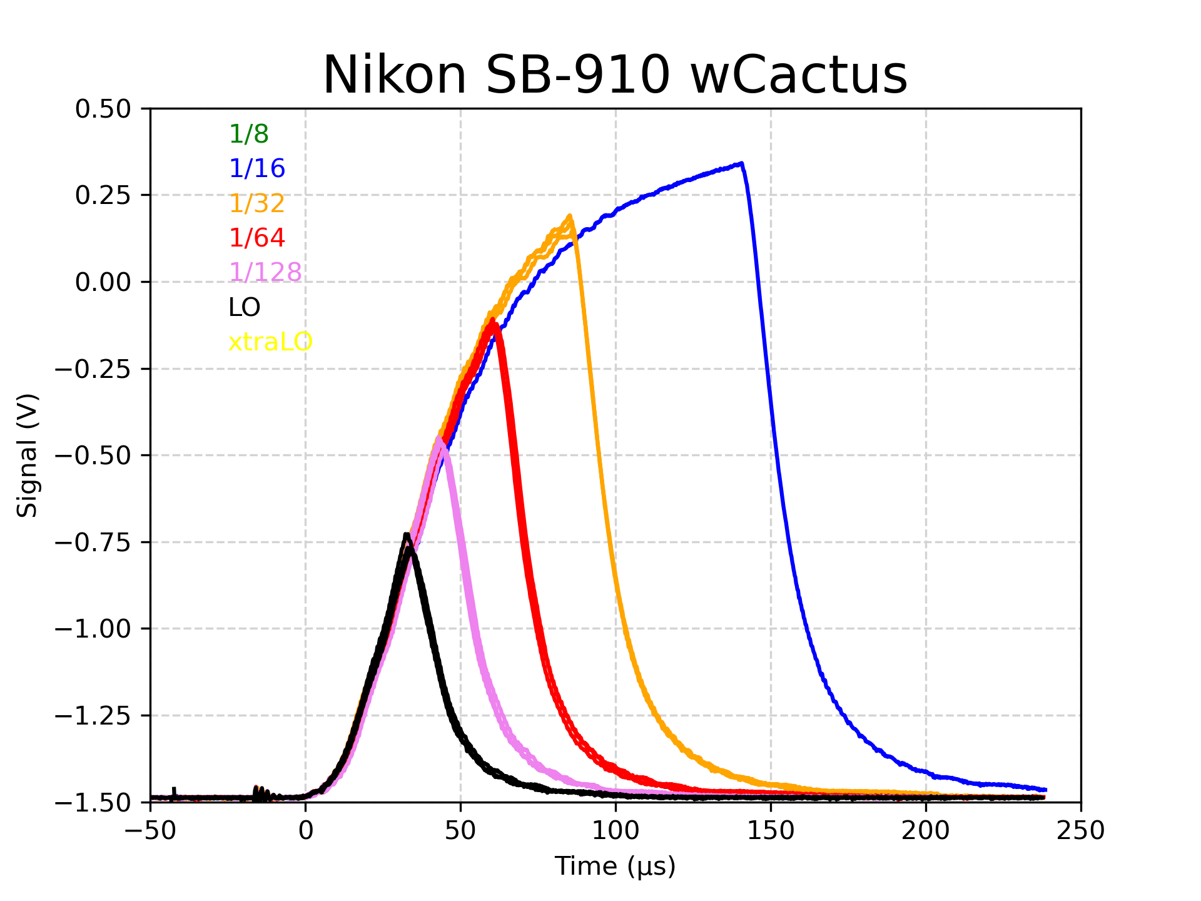
Test Data/2020-08-01/Traces/_MODEL Nikon SB-910 wCactus.png
