td0g/high_speed_flash/Test Data/2020-08-01/Traces/_POWER 5.png

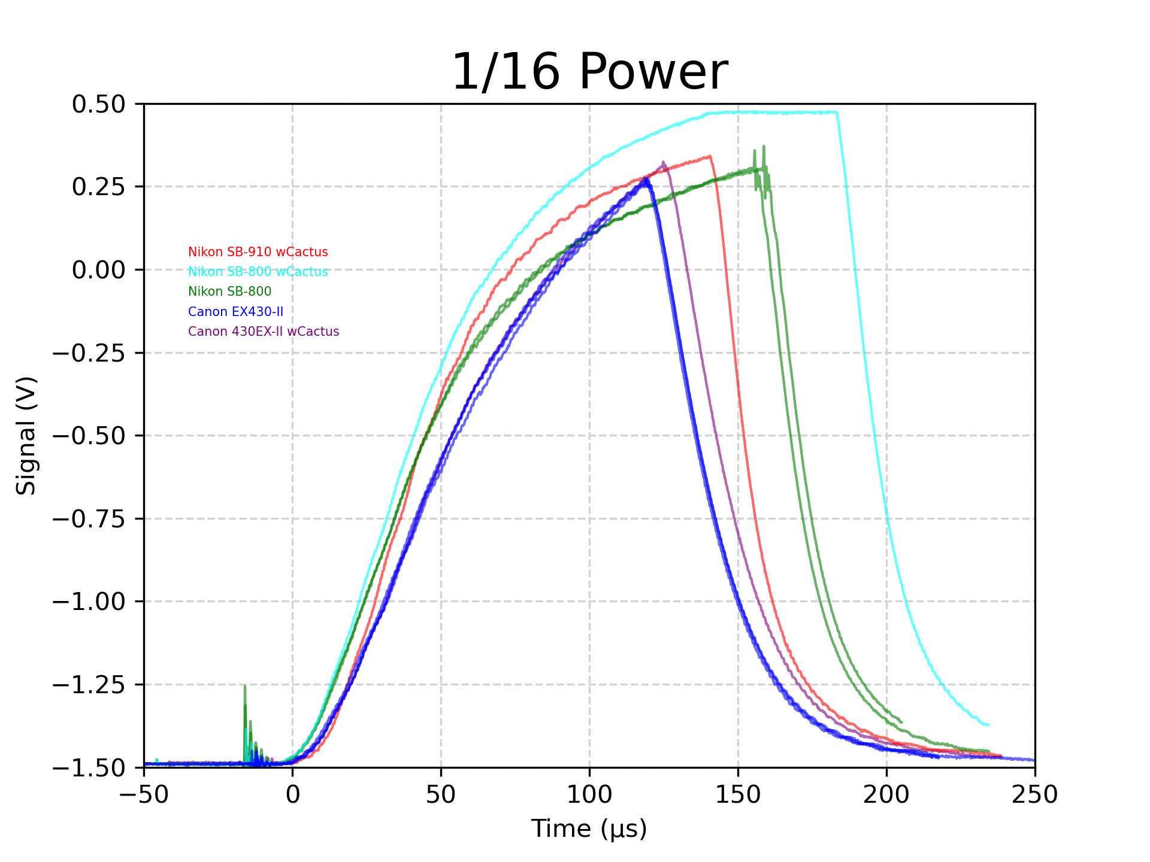
Test Data/2020-08-01/Traces/_POWER 5.png
