td0g/high_speed_flash/Test Data/2020-08-01/Yongnuo Test/115_Yongnuo YN-460II #2_128_2.png

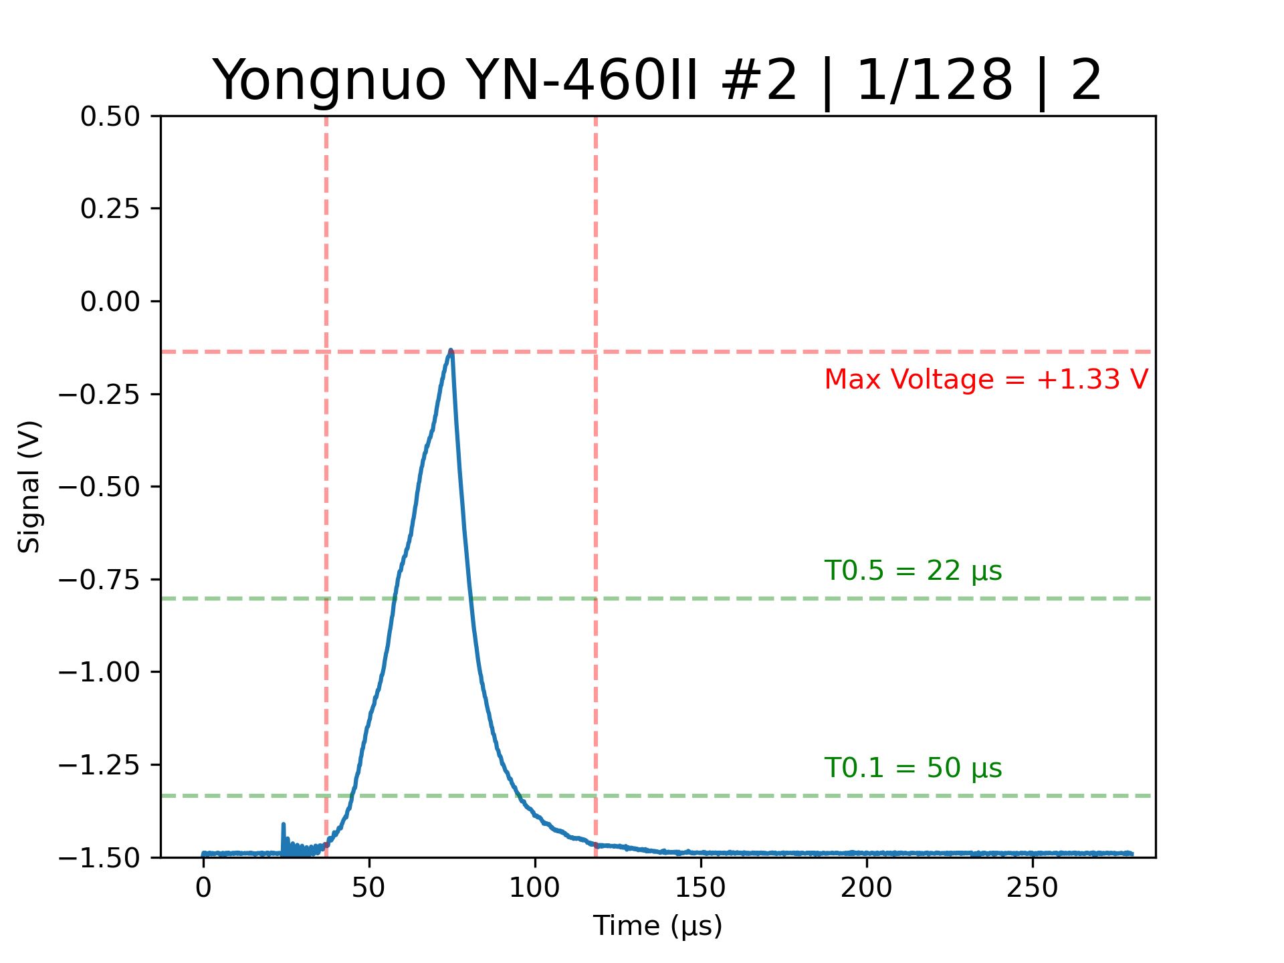
Test Data/2020-08-01/Yongnuo Test/115_Yongnuo YN-460II #2_128_2.png
