td0g/high_speed_flash/Test Data/2020-08-01/Yongnuo Test/117_Yongnuo YN-460II #2_64_1.png

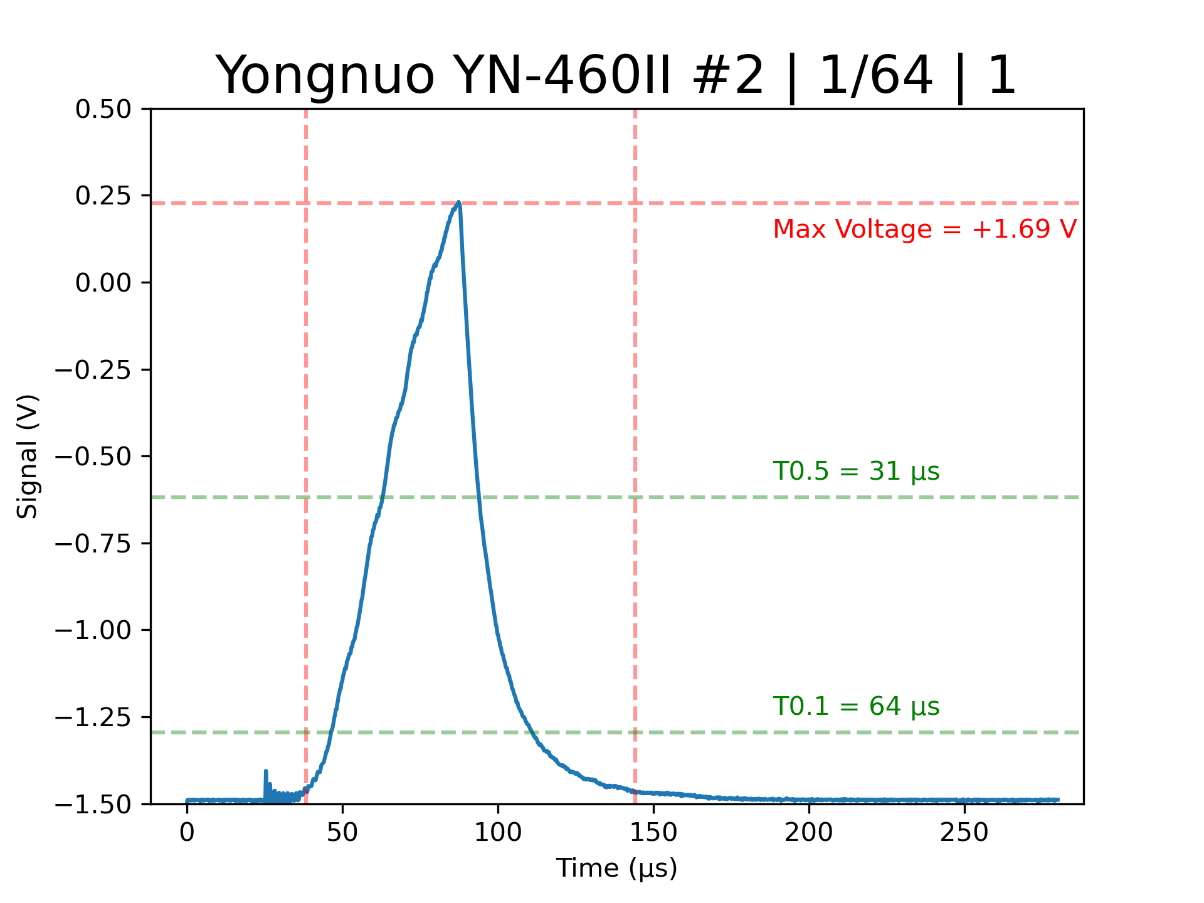
Test Data/2020-08-01/Yongnuo Test/117_Yongnuo YN-460II #2_64_1.png
