td0g/high_speed_flash/MK2/E2-A/Firmware/E2A/_testMacro.ino

/*

void testUnit(){
  while (TRIGGER_HIGH){
    soundDone();
    delay(250);
  }
  for (int i = 0; i < 1000; i++){
    pulseDuration = 0;
    pulseCount = 1;
    forceFlash();
    delay(125);
  }
  while (TRIGGER_HIGH){
    soundDone();
    delay(250);
  }
  for (int i = 0; i < 1000; i++){
    pulseDuration = 1;
    pulseCount = 1;
    forceFlash();
    delay(125);
  }
  while (TRIGGER_HIGH){
    soundDone();
    delay(250);
  }
  for (int i = 0; i < 1000; i++){
    pulseDuration = 2;
    pulseCount = 1;
    forceFlash();
    delay(125);
  }
  while (TRIGGER_HIGH){
    soundDone();
    delay(250);
  }
  for (int i = 0; i < 1000; i++){
    pulseDuration = 3;
    pulseCount = 1;
    forceFlash();
    delay(125);
  }

  
  while (TRIGGER_HIGH){
    soundDone();
    delay(250);
  }
  for (int i = 0; i < 250; i++){
    pulseDuration = 0;
    pulseCount = 6;
    pulseRate = 0;
    forceFlash();
    delay(500);
  }
  
  while (TRIGGER_HIGH){
    soundDone();
    delay(250);
  }
  for (int i = 0; i < 250; i++){
    pulseDuration = 1;
    pulseCount = 4;
    pulseRate = 0;
    forceFlash();
    delay(500);
  }
  
  while (TRIGGER_HIGH){
    soundDone();
    delay(250);
  }
  for (int i = 0; i < 250; i++){
    pulseDuration = 2;
    pulseCount = 4;
    pulseRate = 3;
    forceFlash();
    delay(500);
  }
  
  while (TRIGGER_HIGH){
    soundDone();
    delay(250);
  }
  for (int i = 0; i < 250; i++){
    pulseDuration = 3;
    pulseCount = 3;
    pulseRate = 3;
    forceFlash();
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
        for (byte i = 1; i < pulseCount; i++){         
      while(TCNT1 > _t){};
      while (TCNT1 < _t){};
          FLASH_ON;
          DELAY_4US;
          FLASH_OFF;
          _t += delayTime[pulseRate];
        }
    break;
      default:
      break;
    }
  FLASH_OFF;
}
*/
